sparkfun/Spectacle_Motion_Board/Firmware/Spectacle_Servo_Control_Board/Spectacle_Servo_Control_Board.cydsn/codegentemp/EZI2C_PINS.h

/***************************************************************************//**
* \file EZI2C_PINS.h
* \version 3.20
*
* \brief
*  This file provides constants and parameter values for the pin components
*  buried into SCB Component.
*
* Note:
*
********************************************************************************
* \copyright
* Copyright 2013-2016, Cypress Semiconductor Corporation.  All rights reserved.
* You may use this file only in accordance with the license, terms, conditions,
* disclaimers, and limitations in the end user license agreement accompanying
* the software package with which this file was provided.
*******************************************************************************/

#if !defined(CY_SCB_PINS_EZI2C_H)
#define CY_SCB_PINS_EZI2C_H

#include "cydevice_trm.h"
#include "cyfitter.h"
#include "cytypes.h"


/***************************************
*   Conditional Compilation Parameters
****************************************/

/* Unconfigured pins */
#define EZI2C_REMOVE_RX_WAKE_SCL_MOSI_PIN  (1u)
#define EZI2C_REMOVE_RX_SCL_MOSI_PIN      (1u)
#define EZI2C_REMOVE_TX_SDA_MISO_PIN      (1u)
#define EZI2C_REMOVE_CTS_SCLK_PIN      (1u)
#define EZI2C_REMOVE_RTS_SS0_PIN      (1u)
#define EZI2C_REMOVE_SS1_PIN                 (1u)
#define EZI2C_REMOVE_SS2_PIN                 (1u)
#define EZI2C_REMOVE_SS3_PIN                 (1u)

/* Mode defined pins */
#define EZI2C_REMOVE_I2C_PINS                (0u)
#define EZI2C_REMOVE_SPI_MASTER_PINS         (1u)
#define EZI2C_REMOVE_SPI_MASTER_SCLK_PIN     (1u)
#define EZI2C_REMOVE_SPI_MASTER_MOSI_PIN     (1u)
#define EZI2C_REMOVE_SPI_MASTER_MISO_PIN     (1u)
#define EZI2C_REMOVE_SPI_MASTER_SS0_PIN      (1u)
#define EZI2C_REMOVE_SPI_MASTER_SS1_PIN      (1u)
#define EZI2C_REMOVE_SPI_MASTER_SS2_PIN      (1u)
#define EZI2C_REMOVE_SPI_MASTER_SS3_PIN      (1u)
#define EZI2C_REMOVE_SPI_SLAVE_PINS          (1u)
#define EZI2C_REMOVE_SPI_SLAVE_MOSI_PIN      (1u)
#define EZI2C_REMOVE_SPI_SLAVE_MISO_PIN      (1u)
#define EZI2C_REMOVE_UART_TX_PIN             (1u)
#define EZI2C_REMOVE_UART_RX_TX_PIN          (1u)
#define EZI2C_REMOVE_UART_RX_PIN             (1u)
#define EZI2C_REMOVE_UART_RX_WAKE_PIN        (1u)
#define EZI2C_REMOVE_UART_RTS_PIN            (1u)
#define EZI2C_REMOVE_UART_CTS_PIN            (1u)

/* Unconfigured pins */
#define EZI2C_RX_WAKE_SCL_MOSI_PIN (0u == EZI2C_REMOVE_RX_WAKE_SCL_MOSI_PIN)
#define EZI2C_RX_SCL_MOSI_PIN     (0u == EZI2C_REMOVE_RX_SCL_MOSI_PIN)
#define EZI2C_TX_SDA_MISO_PIN     (0u == EZI2C_REMOVE_TX_SDA_MISO_PIN)
#define EZI2C_CTS_SCLK_PIN     (0u == EZI2C_REMOVE_CTS_SCLK_PIN)
#define EZI2C_RTS_SS0_PIN     (0u == EZI2C_REMOVE_RTS_SS0_PIN)
#define EZI2C_SS1_PIN                (0u == EZI2C_REMOVE_SS1_PIN)
#define EZI2C_SS2_PIN                (0u == EZI2C_REMOVE_SS2_PIN)
#define EZI2C_SS3_PIN                (0u == EZI2C_REMOVE_SS3_PIN)

/* Mode defined pins */
#define EZI2C_I2C_PINS               (0u == EZI2C_REMOVE_I2C_PINS)
#define EZI2C_SPI_MASTER_PINS        (0u == EZI2C_REMOVE_SPI_MASTER_PINS)
#define EZI2C_SPI_MASTER_SCLK_PIN    (0u == EZI2C_REMOVE_SPI_MASTER_SCLK_PIN)
#define EZI2C_SPI_MASTER_MOSI_PIN    (0u == EZI2C_REMOVE_SPI_MASTER_MOSI_PIN)
#define EZI2C_SPI_MASTER_MISO_PIN    (0u == EZI2C_REMOVE_SPI_MASTER_MISO_PIN)
#define EZI2C_SPI_MASTER_SS0_PIN     (0u == EZI2C_REMOVE_SPI_MASTER_SS0_PIN)
#define EZI2C_SPI_MASTER_SS1_PIN     (0u == EZI2C_REMOVE_SPI_MASTER_SS1_PIN)
#define EZI2C_SPI_MASTER_SS2_PIN     (0u == EZI2C_REMOVE_SPI_MASTER_SS2_PIN)
#define EZI2C_SPI_MASTER_SS3_PIN     (0u == EZI2C_REMOVE_SPI_MASTER_SS3_PIN)
#define EZI2C_SPI_SLAVE_PINS         (0u == EZI2C_REMOVE_SPI_SLAVE_PINS)
#define EZI2C_SPI_SLAVE_MOSI_PIN     (0u == EZI2C_REMOVE_SPI_SLAVE_MOSI_PIN)
#define EZI2C_SPI_SLAVE_MISO_PIN     (0u == EZI2C_REMOVE_SPI_SLAVE_MISO_PIN)
#define EZI2C_UART_TX_PIN            (0u == EZI2C_REMOVE_UART_TX_PIN)
#define EZI2C_UART_RX_TX_PIN         (0u == EZI2C_REMOVE_UART_RX_TX_PIN)
#define EZI2C_UART_RX_PIN            (0u == EZI2C_REMOVE_UART_RX_PIN)
#define EZI2C_UART_RX_WAKE_PIN       (0u == EZI2C_REMOVE_UART_RX_WAKE_PIN)
#define EZI2C_UART_RTS_PIN           (0u == EZI2C_REMOVE_UART_RTS_PIN)
#define EZI2C_UART_CTS_PIN           (0u == EZI2C_REMOVE_UART_CTS_PIN)


/***************************************
*             Includes
****************************************/

#if (EZI2C_RX_WAKE_SCL_MOSI_PIN)
    #include "EZI2C_uart_rx_wake_i2c_scl_spi_mosi.h"
#endif /* (EZI2C_RX_SCL_MOSI) */

#if (EZI2C_RX_SCL_MOSI_PIN)
    #include "EZI2C_uart_rx_i2c_scl_spi_mosi.h"
#endif /* (EZI2C_RX_SCL_MOSI) */

#if (EZI2C_TX_SDA_MISO_PIN)
    #include "EZI2C_uart_tx_i2c_sda_spi_miso.h"
#endif /* (EZI2C_TX_SDA_MISO) */

#if (EZI2C_CTS_SCLK_PIN)
    #include "EZI2C_uart_cts_spi_sclk.h"
#endif /* (EZI2C_CTS_SCLK) */

#if (EZI2C_RTS_SS0_PIN)
    #include "EZI2C_uart_rts_spi_ss0.h"
#endif /* (EZI2C_RTS_SS0_PIN) */

#if (EZI2C_SS1_PIN)
    #include "EZI2C_spi_ss1.h"
#endif /* (EZI2C_SS1_PIN) */

#if (EZI2C_SS2_PIN)
    #include "EZI2C_spi_ss2.h"
#endif /* (EZI2C_SS2_PIN) */

#if (EZI2C_SS3_PIN)
    #include "EZI2C_spi_ss3.h"
#endif /* (EZI2C_SS3_PIN) */

#if (EZI2C_I2C_PINS)
    #include "EZI2C_scl.h"
    #include "EZI2C_sda.h"
#endif /* (EZI2C_I2C_PINS) */

#if (EZI2C_SPI_MASTER_PINS)
#if (EZI2C_SPI_MASTER_SCLK_PIN)
    #include "EZI2C_sclk_m.h"
#endif /* (EZI2C_SPI_MASTER_SCLK_PIN) */

#if (EZI2C_SPI_MASTER_MOSI_PIN)
    #include "EZI2C_mosi_m.h"
#endif /* (EZI2C_SPI_MASTER_MOSI_PIN) */

#if (EZI2C_SPI_MASTER_MISO_PIN)
    #include "EZI2C_miso_m.h"
#endif /*(EZI2C_SPI_MASTER_MISO_PIN) */
#endif /* (EZI2C_SPI_MASTER_PINS) */

#if (EZI2C_SPI_SLAVE_PINS)
    #include "EZI2C_sclk_s.h"
    #include "EZI2C_ss_s.h"

#if (EZI2C_SPI_SLAVE_MOSI_PIN)
    #include "EZI2C_mosi_s.h"
#endif /* (EZI2C_SPI_SLAVE_MOSI_PIN) */

#if (EZI2C_SPI_SLAVE_MISO_PIN)
    #include "EZI2C_miso_s.h"
#endif /*(EZI2C_SPI_SLAVE_MISO_PIN) */
#endif /* (EZI2C_SPI_SLAVE_PINS) */

#if (EZI2C_SPI_MASTER_SS0_PIN)
    #include "EZI2C_ss0_m.h"
#endif /* (EZI2C_SPI_MASTER_SS0_PIN) */

#if (EZI2C_SPI_MASTER_SS1_PIN)
    #include "EZI2C_ss1_m.h"
#endif /* (EZI2C_SPI_MASTER_SS1_PIN) */

#if (EZI2C_SPI_MASTER_SS2_PIN)
    #include "EZI2C_ss2_m.h"
#endif /* (EZI2C_SPI_MASTER_SS2_PIN) */

#if (EZI2C_SPI_MASTER_SS3_PIN)
    #include "EZI2C_ss3_m.h"
#endif /* (EZI2C_SPI_MASTER_SS3_PIN) */

#if (EZI2C_UART_TX_PIN)
    #include "EZI2C_tx.h"
#endif /* (EZI2C_UART_TX_PIN) */

#if (EZI2C_UART_RX_TX_PIN)
    #include "EZI2C_rx_tx.h"
#endif /* (EZI2C_UART_RX_TX_PIN) */

#if (EZI2C_UART_RX_PIN)
    #include "EZI2C_rx.h"
#endif /* (EZI2C_UART_RX_PIN) */

#if (EZI2C_UART_RX_WAKE_PIN)
    #include "EZI2C_rx_wake.h"
#endif /* (EZI2C_UART_RX_WAKE_PIN) */

#if (EZI2C_UART_RTS_PIN)
    #include "EZI2C_rts.h"
#endif /* (EZI2C_UART_RTS_PIN) */

#if (EZI2C_UART_CTS_PIN)
    #include "EZI2C_cts.h"
#endif /* (EZI2C_UART_CTS_PIN) */


/***************************************
*              Registers
***************************************/

#if (EZI2C_RX_SCL_MOSI_PIN)
    #define EZI2C_RX_SCL_MOSI_HSIOM_REG   (*(reg32 *) EZI2C_uart_rx_i2c_scl_spi_mosi__0__HSIOM)
    #define EZI2C_RX_SCL_MOSI_HSIOM_PTR   ( (reg32 *) EZI2C_uart_rx_i2c_scl_spi_mosi__0__HSIOM)
    
    #define EZI2C_RX_SCL_MOSI_HSIOM_MASK      (EZI2C_uart_rx_i2c_scl_spi_mosi__0__HSIOM_MASK)
    #define EZI2C_RX_SCL_MOSI_HSIOM_POS       (EZI2C_uart_rx_i2c_scl_spi_mosi__0__HSIOM_SHIFT)
    #define EZI2C_RX_SCL_MOSI_HSIOM_SEL_GPIO  (EZI2C_uart_rx_i2c_scl_spi_mosi__0__HSIOM_GPIO)
    #define EZI2C_RX_SCL_MOSI_HSIOM_SEL_I2C   (EZI2C_uart_rx_i2c_scl_spi_mosi__0__HSIOM_I2C)
    #define EZI2C_RX_SCL_MOSI_HSIOM_SEL_SPI   (EZI2C_uart_rx_i2c_scl_spi_mosi__0__HSIOM_SPI)
    #define EZI2C_RX_SCL_MOSI_HSIOM_SEL_UART  (EZI2C_uart_rx_i2c_scl_spi_mosi__0__HSIOM_UART)
    
#elif (EZI2C_RX_WAKE_SCL_MOSI_PIN)
    #define EZI2C_RX_WAKE_SCL_MOSI_HSIOM_REG   (*(reg32 *) EZI2C_uart_rx_wake_i2c_scl_spi_mosi__0__HSIOM)
    #define EZI2C_RX_WAKE_SCL_MOSI_HSIOM_PTR   ( (reg32 *) EZI2C_uart_rx_wake_i2c_scl_spi_mosi__0__HSIOM)
    
    #define EZI2C_RX_WAKE_SCL_MOSI_HSIOM_MASK      (EZI2C_uart_rx_wake_i2c_scl_spi_mosi__0__HSIOM_MASK)
    #define EZI2C_RX_WAKE_SCL_MOSI_HSIOM_POS       (EZI2C_uart_rx_wake_i2c_scl_spi_mosi__0__HSIOM_SHIFT)
    #define EZI2C_RX_WAKE_SCL_MOSI_HSIOM_SEL_GPIO  (EZI2C_uart_rx_wake_i2c_scl_spi_mosi__0__HSIOM_GPIO)
    #define EZI2C_RX_WAKE_SCL_MOSI_HSIOM_SEL_I2C   (EZI2C_uart_rx_wake_i2c_scl_spi_mosi__0__HSIOM_I2C)
    #define EZI2C_RX_WAKE_SCL_MOSI_HSIOM_SEL_SPI   (EZI2C_uart_rx_wake_i2c_scl_spi_mosi__0__HSIOM_SPI)
    #define EZI2C_RX_WAKE_SCL_MOSI_HSIOM_SEL_UART  (EZI2C_uart_rx_wake_i2c_scl_spi_mosi__0__HSIOM_UART)    
   
    #define EZI2C_RX_WAKE_SCL_MOSI_INTCFG_REG (*(reg32 *) EZI2C_uart_rx_wake_i2c_scl_spi_mosi__0__INTCFG)
    #define EZI2C_RX_WAKE_SCL_MOSI_INTCFG_PTR ( (reg32 *) EZI2C_uart_rx_wake_i2c_scl_spi_mosi__0__INTCFG)
    #define EZI2C_RX_WAKE_SCL_MOSI_INTCFG_TYPE_POS  (EZI2C_uart_rx_wake_i2c_scl_spi_mosi__SHIFT)
    #define EZI2C_RX_WAKE_SCL_MOSI_INTCFG_TYPE_MASK ((uint32) EZI2C_INTCFG_TYPE_MASK << \
                                                                           EZI2C_RX_WAKE_SCL_MOSI_INTCFG_TYPE_POS)
#else
    /* None of pins EZI2C_RX_SCL_MOSI_PIN or EZI2C_RX_WAKE_SCL_MOSI_PIN present.*/
#endif /* (EZI2C_RX_SCL_MOSI_PIN) */

#if (EZI2C_TX_SDA_MISO_PIN)
    #define EZI2C_TX_SDA_MISO_HSIOM_REG   (*(reg32 *) EZI2C_uart_tx_i2c_sda_spi_miso__0__HSIOM)
    #define EZI2C_TX_SDA_MISO_HSIOM_PTR   ( (reg32 *) EZI2C_uart_tx_i2c_sda_spi_miso__0__HSIOM)
    
    #define EZI2C_TX_SDA_MISO_HSIOM_MASK      (EZI2C_uart_tx_i2c_sda_spi_miso__0__HSIOM_MASK)
    #define EZI2C_TX_SDA_MISO_HSIOM_POS       (EZI2C_uart_tx_i2c_sda_spi_miso__0__HSIOM_SHIFT)
    #define EZI2C_TX_SDA_MISO_HSIOM_SEL_GPIO  (EZI2C_uart_tx_i2c_sda_spi_miso__0__HSIOM_GPIO)
    #define EZI2C_TX_SDA_MISO_HSIOM_SEL_I2C   (EZI2C_uart_tx_i2c_sda_spi_miso__0__HSIOM_I2C)
    #define EZI2C_TX_SDA_MISO_HSIOM_SEL_SPI   (EZI2C_uart_tx_i2c_sda_spi_miso__0__HSIOM_SPI)
    #define EZI2C_TX_SDA_MISO_HSIOM_SEL_UART  (EZI2C_uart_tx_i2c_sda_spi_miso__0__HSIOM_UART)
#endif /* (EZI2C_TX_SDA_MISO_PIN) */

#if (EZI2C_CTS_SCLK_PIN)
    #define EZI2C_CTS_SCLK_HSIOM_REG   (*(reg32 *) EZI2C_uart_cts_spi_sclk__0__HSIOM)
    #define EZI2C_CTS_SCLK_HSIOM_PTR   ( (reg32 *) EZI2C_uart_cts_spi_sclk__0__HSIOM)
    
    #define EZI2C_CTS_SCLK_HSIOM_MASK      (EZI2C_uart_cts_spi_sclk__0__HSIOM_MASK)
    #define EZI2C_CTS_SCLK_HSIOM_POS       (EZI2C_uart_cts_spi_sclk__0__HSIOM_SHIFT)
    #define EZI2C_CTS_SCLK_HSIOM_SEL_GPIO  (EZI2C_uart_cts_spi_sclk__0__HSIOM_GPIO)
    #define EZI2C_CTS_SCLK_HSIOM_SEL_I2C   (EZI2C_uart_cts_spi_sclk__0__HSIOM_I2C)
    #define EZI2C_CTS_SCLK_HSIOM_SEL_SPI   (EZI2C_uart_cts_spi_sclk__0__HSIOM_SPI)
    #define EZI2C_CTS_SCLK_HSIOM_SEL_UART  (EZI2C_uart_cts_spi_sclk__0__HSIOM_UART)
#endif /* (EZI2C_CTS_SCLK_PIN) */

#if (EZI2C_RTS_SS0_PIN)
    #define EZI2C_RTS_SS0_HSIOM_REG   (*(reg32 *) EZI2C_uart_rts_spi_ss0__0__HSIOM)
    #define EZI2C_RTS_SS0_HSIOM_PTR   ( (reg32 *) EZI2C_uart_rts_spi_ss0__0__HSIOM)
    
    #define EZI2C_RTS_SS0_HSIOM_MASK      (EZI2C_uart_rts_spi_ss0__0__HSIOM_MASK)
    #define EZI2C_RTS_SS0_HSIOM_POS       (EZI2C_uart_rts_spi_ss0__0__HSIOM_SHIFT)
    #define EZI2C_RTS_SS0_HSIOM_SEL_GPIO  (EZI2C_uart_rts_spi_ss0__0__HSIOM_GPIO)
    #define EZI2C_RTS_SS0_HSIOM_SEL_I2C   (EZI2C_uart_rts_spi_ss0__0__HSIOM_I2C)
    #define EZI2C_RTS_SS0_HSIOM_SEL_SPI   (EZI2C_uart_rts_spi_ss0__0__HSIOM_SPI)
#if !(EZI2C_CY_SCBIP_V0 || EZI2C_CY_SCBIP_V1)
    #define EZI2C_RTS_SS0_HSIOM_SEL_UART  (EZI2C_uart_rts_spi_ss0__0__HSIOM_UART)
#endif /* !(EZI2C_CY_SCBIP_V0 || EZI2C_CY_SCBIP_V1) */
#endif /* (EZI2C_RTS_SS0_PIN) */

#if (EZI2C_SS1_PIN)
    #define EZI2C_SS1_HSIOM_REG  (*(reg32 *) EZI2C_spi_ss1__0__HSIOM)
    #define EZI2C_SS1_HSIOM_PTR  ( (reg32 *) EZI2C_spi_ss1__0__HSIOM)
    
    #define EZI2C_SS1_HSIOM_MASK     (EZI2C_spi_ss1__0__HSIOM_MASK)
    #define EZI2C_SS1_HSIOM_POS      (EZI2C_spi_ss1__0__HSIOM_SHIFT)
    #define EZI2C_SS1_HSIOM_SEL_GPIO (EZI2C_spi_ss1__0__HSIOM_GPIO)
    #define EZI2C_SS1_HSIOM_SEL_I2C  (EZI2C_spi_ss1__0__HSIOM_I2C)
    #define EZI2C_SS1_HSIOM_SEL_SPI  (EZI2C_spi_ss1__0__HSIOM_SPI)
#endif /* (EZI2C_SS1_PIN) */

#if (EZI2C_SS2_PIN)
    #define EZI2C_SS2_HSIOM_REG     (*(reg32 *) EZI2C_spi_ss2__0__HSIOM)
    #define EZI2C_SS2_HSIOM_PTR     ( (reg32 *) EZI2C_spi_ss2__0__HSIOM)
    
    #define EZI2C_SS2_HSIOM_MASK     (EZI2C_spi_ss2__0__HSIOM_MASK)
    #define EZI2C_SS2_HSIOM_POS      (EZI2C_spi_ss2__0__HSIOM_SHIFT)
    #define EZI2C_SS2_HSIOM_SEL_GPIO (EZI2C_spi_ss2__0__HSIOM_GPIO)
    #define EZI2C_SS2_HSIOM_SEL_I2C  (EZI2C_spi_ss2__0__HSIOM_I2C)
    #define EZI2C_SS2_HSIOM_SEL_SPI  (EZI2C_spi_ss2__0__HSIOM_SPI)
#endif /* (EZI2C_SS2_PIN) */

#if (EZI2C_SS3_PIN)
    #define EZI2C_SS3_HSIOM_REG     (*(reg32 *) EZI2C_spi_ss3__0__HSIOM)
    #define EZI2C_SS3_HSIOM_PTR     ( (reg32 *) EZI2C_spi_ss3__0__HSIOM)
    
    #define EZI2C_SS3_HSIOM_MASK     (EZI2C_spi_ss3__0__HSIOM_MASK)
    #define EZI2C_SS3_HSIOM_POS      (EZI2C_spi_ss3__0__HSIOM_SHIFT)
    #define EZI2C_SS3_HSIOM_SEL_GPIO (EZI2C_spi_ss3__0__HSIOM_GPIO)
    #define EZI2C_SS3_HSIOM_SEL_I2C  (EZI2C_spi_ss3__0__HSIOM_I2C)
    #define EZI2C_SS3_HSIOM_SEL_SPI  (EZI2C_spi_ss3__0__HSIOM_SPI)
#endif /* (EZI2C_SS3_PIN) */

#if (EZI2C_I2C_PINS)
    #define EZI2C_SCL_HSIOM_REG  (*(reg32 *) EZI2C_scl__0__HSIOM)
    #define EZI2C_SCL_HSIOM_PTR  ( (reg32 *) EZI2C_scl__0__HSIOM)
    
    #define EZI2C_SCL_HSIOM_MASK     (EZI2C_scl__0__HSIOM_MASK)
    #define EZI2C_SCL_HSIOM_POS      (EZI2C_scl__0__HSIOM_SHIFT)
    #define EZI2C_SCL_HSIOM_SEL_GPIO (EZI2C_sda__0__HSIOM_GPIO)
    #define EZI2C_SCL_HSIOM_SEL_I2C  (EZI2C_sda__0__HSIOM_I2C)
    
    #define EZI2C_SDA_HSIOM_REG  (*(reg32 *) EZI2C_sda__0__HSIOM)
    #define EZI2C_SDA_HSIOM_PTR  ( (reg32 *) EZI2C_sda__0__HSIOM)
    
    #define EZI2C_SDA_HSIOM_MASK     (EZI2C_sda__0__HSIOM_MASK)
    #define EZI2C_SDA_HSIOM_POS      (EZI2C_sda__0__HSIOM_SHIFT)
    #define EZI2C_SDA_HSIOM_SEL_GPIO (EZI2C_sda__0__HSIOM_GPIO)
    #define EZI2C_SDA_HSIOM_SEL_I2C  (EZI2C_sda__0__HSIOM_I2C)
#endif /* (EZI2C_I2C_PINS) */

#if (EZI2C_SPI_SLAVE_PINS)
    #define EZI2C_SCLK_S_HSIOM_REG   (*(reg32 *) EZI2C_sclk_s__0__HSIOM)
    #define EZI2C_SCLK_S_HSIOM_PTR   ( (reg32 *) EZI2C_sclk_s__0__HSIOM)
    
    #define EZI2C_SCLK_S_HSIOM_MASK      (EZI2C_sclk_s__0__HSIOM_MASK)
    #define EZI2C_SCLK_S_HSIOM_POS       (EZI2C_sclk_s__0__HSIOM_SHIFT)
    #define EZI2C_SCLK_S_HSIOM_SEL_GPIO  (EZI2C_sclk_s__0__HSIOM_GPIO)
    #define EZI2C_SCLK_S_HSIOM_SEL_SPI   (EZI2C_sclk_s__0__HSIOM_SPI)
    
    #define EZI2C_SS0_S_HSIOM_REG    (*(reg32 *) EZI2C_ss0_s__0__HSIOM)
    #define EZI2C_SS0_S_HSIOM_PTR    ( (reg32 *) EZI2C_ss0_s__0__HSIOM)
    
    #define EZI2C_SS0_S_HSIOM_MASK       (EZI2C_ss0_s__0__HSIOM_MASK)
    #define EZI2C_SS0_S_HSIOM_POS        (EZI2C_ss0_s__0__HSIOM_SHIFT)
    #define EZI2C_SS0_S_HSIOM_SEL_GPIO   (EZI2C_ss0_s__0__HSIOM_GPIO)  
    #define EZI2C_SS0_S_HSIOM_SEL_SPI    (EZI2C_ss0_s__0__HSIOM_SPI)
#endif /* (EZI2C_SPI_SLAVE_PINS) */

#if (EZI2C_SPI_SLAVE_MOSI_PIN)
    #define EZI2C_MOSI_S_HSIOM_REG   (*(reg32 *) EZI2C_mosi_s__0__HSIOM)
    #define EZI2C_MOSI_S_HSIOM_PTR   ( (reg32 *) EZI2C_mosi_s__0__HSIOM)
    
    #define EZI2C_MOSI_S_HSIOM_MASK      (EZI2C_mosi_s__0__HSIOM_MASK)
    #define EZI2C_MOSI_S_HSIOM_POS       (EZI2C_mosi_s__0__HSIOM_SHIFT)
    #define EZI2C_MOSI_S_HSIOM_SEL_GPIO  (EZI2C_mosi_s__0__HSIOM_GPIO)
    #define EZI2C_MOSI_S_HSIOM_SEL_SPI   (EZI2C_mosi_s__0__HSIOM_SPI)
#endif /* (EZI2C_SPI_SLAVE_MOSI_PIN) */

#if (EZI2C_SPI_SLAVE_MISO_PIN)
    #define EZI2C_MISO_S_HSIOM_REG   (*(reg32 *) EZI2C_miso_s__0__HSIOM)
    #define EZI2C_MISO_S_HSIOM_PTR   ( (reg32 *) EZI2C_miso_s__0__HSIOM)
    
    #define EZI2C_MISO_S_HSIOM_MASK      (EZI2C_miso_s__0__HSIOM_MASK)
    #define EZI2C_MISO_S_HSIOM_POS       (EZI2C_miso_s__0__HSIOM_SHIFT)
    #define EZI2C_MISO_S_HSIOM_SEL_GPIO  (EZI2C_miso_s__0__HSIOM_GPIO)
    #define EZI2C_MISO_S_HSIOM_SEL_SPI   (EZI2C_miso_s__0__HSIOM_SPI)
#endif /* (EZI2C_SPI_SLAVE_MISO_PIN) */

#if (EZI2C_SPI_MASTER_MISO_PIN)
    #define EZI2C_MISO_M_HSIOM_REG   (*(reg32 *) EZI2C_miso_m__0__HSIOM)
    #define EZI2C_MISO_M_HSIOM_PTR   ( (reg32 *) EZI2C_miso_m__0__HSIOM)
    
    #define EZI2C_MISO_M_HSIOM_MASK      (EZI2C_miso_m__0__HSIOM_MASK)
    #define EZI2C_MISO_M_HSIOM_POS       (EZI2C_miso_m__0__HSIOM_SHIFT)
    #define EZI2C_MISO_M_HSIOM_SEL_GPIO  (EZI2C_miso_m__0__HSIOM_GPIO)
    #define EZI2C_MISO_M_HSIOM_SEL_SPI   (EZI2C_miso_m__0__HSIOM_SPI)
#endif /* (EZI2C_SPI_MASTER_MISO_PIN) */

#if (EZI2C_SPI_MASTER_MOSI_PIN)
    #define EZI2C_MOSI_M_HSIOM_REG   (*(reg32 *) EZI2C_mosi_m__0__HSIOM)
    #define EZI2C_MOSI_M_HSIOM_PTR   ( (reg32 *) EZI2C_mosi_m__0__HSIOM)
    
    #define EZI2C_MOSI_M_HSIOM_MASK      (EZI2C_mosi_m__0__HSIOM_MASK)
    #define EZI2C_MOSI_M_HSIOM_POS       (EZI2C_mosi_m__0__HSIOM_SHIFT)
    #define EZI2C_MOSI_M_HSIOM_SEL_GPIO  (EZI2C_mosi_m__0__HSIOM_GPIO)
    #define EZI2C_MOSI_M_HSIOM_SEL_SPI   (EZI2C_mosi_m__0__HSIOM_SPI)
#endif /* (EZI2C_SPI_MASTER_MOSI_PIN) */

#if (EZI2C_SPI_MASTER_SCLK_PIN)
    #define EZI2C_SCLK_M_HSIOM_REG   (*(reg32 *) EZI2C_sclk_m__0__HSIOM)
    #define EZI2C_SCLK_M_HSIOM_PTR   ( (reg32 *) EZI2C_sclk_m__0__HSIOM)
    
    #define EZI2C_SCLK_M_HSIOM_MASK      (EZI2C_sclk_m__0__HSIOM_MASK)
    #define EZI2C_SCLK_M_HSIOM_POS       (EZI2C_sclk_m__0__HSIOM_SHIFT)
    #define EZI2C_SCLK_M_HSIOM_SEL_GPIO  (EZI2C_sclk_m__0__HSIOM_GPIO)
    #define EZI2C_SCLK_M_HSIOM_SEL_SPI   (EZI2C_sclk_m__0__HSIOM_SPI)
#endif /* (EZI2C_SPI_MASTER_SCLK_PIN) */

#if (EZI2C_SPI_MASTER_SS0_PIN)
    #define EZI2C_SS0_M_HSIOM_REG    (*(reg32 *) EZI2C_ss0_m__0__HSIOM)
    #define EZI2C_SS0_M_HSIOM_PTR    ( (reg32 *) EZI2C_ss0_m__0__HSIOM)
    
    #define EZI2C_SS0_M_HSIOM_MASK       (EZI2C_ss0_m__0__HSIOM_MASK)
    #define EZI2C_SS0_M_HSIOM_POS        (EZI2C_ss0_m__0__HSIOM_SHIFT)
    #define EZI2C_SS0_M_HSIOM_SEL_GPIO   (EZI2C_ss0_m__0__HSIOM_GPIO)
    #define EZI2C_SS0_M_HSIOM_SEL_SPI    (EZI2C_ss0_m__0__HSIOM_SPI)
#endif /* (EZI2C_SPI_MASTER_SS0_PIN) */

#if (EZI2C_SPI_MASTER_SS1_PIN)
    #define EZI2C_SS1_M_HSIOM_REG    (*(reg32 *) EZI2C_ss1_m__0__HSIOM)
    #define EZI2C_SS1_M_HSIOM_PTR    ( (reg32 *) EZI2C_ss1_m__0__HSIOM)
    
    #define EZI2C_SS1_M_HSIOM_MASK       (EZI2C_ss1_m__0__HSIOM_MASK)
    #define EZI2C_SS1_M_HSIOM_POS        (EZI2C_ss1_m__0__HSIOM_SHIFT)
    #define EZI2C_SS1_M_HSIOM_SEL_GPIO   (EZI2C_ss1_m__0__HSIOM_GPIO)
    #define EZI2C_SS1_M_HSIOM_SEL_SPI    (EZI2C_ss1_m__0__HSIOM_SPI)
#endif /* (EZI2C_SPI_MASTER_SS1_PIN) */

#if (EZI2C_SPI_MASTER_SS2_PIN)
    #define EZI2C_SS2_M_HSIOM_REG    (*(reg32 *) EZI2C_ss2_m__0__HSIOM)
    #define EZI2C_SS2_M_HSIOM_PTR    ( (reg32 *) EZI2C_ss2_m__0__HSIOM)
    
    #define EZI2C_SS2_M_HSIOM_MASK       (EZI2C_ss2_m__0__HSIOM_MASK)
    #define EZI2C_SS2_M_HSIOM_POS        (EZI2C_ss2_m__0__HSIOM_SHIFT)
    #define EZI2C_SS2_M_HSIOM_SEL_GPIO   (EZI2C_ss2_m__0__HSIOM_GPIO)
    #define EZI2C_SS2_M_HSIOM_SEL_SPI    (EZI2C_ss2_m__0__HSIOM_SPI)
#endif /* (EZI2C_SPI_MASTER_SS2_PIN) */

#if (EZI2C_SPI_MASTER_SS3_PIN)
    #define EZI2C_SS3_M_HSIOM_REG    (*(reg32 *) EZI2C_ss3_m__0__HSIOM)
    #define EZI2C_SS3_M_HSIOM_PTR    ( (reg32 *) EZI2C_ss3_m__0__HSIOM)
    
    #define EZI2C_SS3_M_HSIOM_MASK      (EZI2C_ss3_m__0__HSIOM_MASK)
    #define EZI2C_SS3_M_HSIOM_POS       (EZI2C_ss3_m__0__HSIOM_SHIFT)
    #define EZI2C_SS3_M_HSIOM_SEL_GPIO  (EZI2C_ss3_m__0__HSIOM_GPIO)
    #define EZI2C_SS3_M_HSIOM_SEL_SPI   (EZI2C_ss3_m__0__HSIOM_SPI)
#endif /* (EZI2C_SPI_MASTER_SS3_PIN) */

#if (EZI2C_UART_RX_PIN)
    #define EZI2C_RX_HSIOM_REG   (*(reg32 *) EZI2C_rx__0__HSIOM)
    #define EZI2C_RX_HSIOM_PTR   ( (reg32 *) EZI2C_rx__0__HSIOM)
    
    #define EZI2C_RX_HSIOM_MASK      (EZI2C_rx__0__HSIOM_MASK)
    #define EZI2C_RX_HSIOM_POS       (EZI2C_rx__0__HSIOM_SHIFT)
    #define EZI2C_RX_HSIOM_SEL_GPIO  (EZI2C_rx__0__HSIOM_GPIO)
    #define EZI2C_RX_HSIOM_SEL_UART  (EZI2C_rx__0__HSIOM_UART)
#endif /* (EZI2C_UART_RX_PIN) */

#if (EZI2C_UART_RX_WAKE_PIN)
    #define EZI2C_RX_WAKE_HSIOM_REG   (*(reg32 *) EZI2C_rx_wake__0__HSIOM)
    #define EZI2C_RX_WAKE_HSIOM_PTR   ( (reg32 *) EZI2C_rx_wake__0__HSIOM)
    
    #define EZI2C_RX_WAKE_HSIOM_MASK      (EZI2C_rx_wake__0__HSIOM_MASK)
    #define EZI2C_RX_WAKE_HSIOM_POS       (EZI2C_rx_wake__0__HSIOM_SHIFT)
    #define EZI2C_RX_WAKE_HSIOM_SEL_GPIO  (EZI2C_rx_wake__0__HSIOM_GPIO)
    #define EZI2C_RX_WAKE_HSIOM_SEL_UART  (EZI2C_rx_wake__0__HSIOM_UART)
#endif /* (EZI2C_UART_WAKE_RX_PIN) */

#if (EZI2C_UART_CTS_PIN)
    #define EZI2C_CTS_HSIOM_REG   (*(reg32 *) EZI2C_cts__0__HSIOM)
    #define EZI2C_CTS_HSIOM_PTR   ( (reg32 *) EZI2C_cts__0__HSIOM)
    
    #define EZI2C_CTS_HSIOM_MASK      (EZI2C_cts__0__HSIOM_MASK)
    #define EZI2C_CTS_HSIOM_POS       (EZI2C_cts__0__HSIOM_SHIFT)
    #define EZI2C_CTS_HSIOM_SEL_GPIO  (EZI2C_cts__0__HSIOM_GPIO)
    #define EZI2C_CTS_HSIOM_SEL_UART  (EZI2C_cts__0__HSIOM_UART)
#endif /* (EZI2C_UART_CTS_PIN) */

#if (EZI2C_UART_TX_PIN)
    #define EZI2C_TX_HSIOM_REG   (*(reg32 *) EZI2C_tx__0__HSIOM)
    #define EZI2C_TX_HSIOM_PTR   ( (reg32 *) EZI2C_tx__0__HSIOM)
    
    #define EZI2C_TX_HSIOM_MASK      (EZI2C_tx__0__HSIOM_MASK)
    #define EZI2C_TX_HSIOM_POS       (EZI2C_tx__0__HSIOM_SHIFT)
    #define EZI2C_TX_HSIOM_SEL_GPIO  (EZI2C_tx__0__HSIOM_GPIO)
    #define EZI2C_TX_HSIOM_SEL_UART  (EZI2C_tx__0__HSIOM_UART)
#endif /* (EZI2C_UART_TX_PIN) */

#if (EZI2C_UART_RX_TX_PIN)
    #define EZI2C_RX_TX_HSIOM_REG   (*(reg32 *) EZI2C_rx_tx__0__HSIOM)
    #define EZI2C_RX_TX_HSIOM_PTR   ( (reg32 *) EZI2C_rx_tx__0__HSIOM)
    
    #define EZI2C_RX_TX_HSIOM_MASK      (EZI2C_rx_tx__0__HSIOM_MASK)
    #define EZI2C_RX_TX_HSIOM_POS       (EZI2C_rx_tx__0__HSIOM_SHIFT)
    #define EZI2C_RX_TX_HSIOM_SEL_GPIO  (EZI2C_rx_tx__0__HSIOM_GPIO)
    #define EZI2C_RX_TX_HSIOM_SEL_UART  (EZI2C_rx_tx__0__HSIOM_UART)
#endif /* (EZI2C_UART_RX_TX_PIN) */

#if (EZI2C_UART_RTS_PIN)
    #define EZI2C_RTS_HSIOM_REG      (*(reg32 *) EZI2C_rts__0__HSIOM)
    #define EZI2C_RTS_HSIOM_PTR      ( (reg32 *) EZI2C_rts__0__HSIOM)
    
    #define EZI2C_RTS_HSIOM_MASK     (EZI2C_rts__0__HSIOM_MASK)
    #define EZI2C_RTS_HSIOM_POS      (EZI2C_rts__0__HSIOM_SHIFT)    
    #define EZI2C_RTS_HSIOM_SEL_GPIO (EZI2C_rts__0__HSIOM_GPIO)
    #define EZI2C_RTS_HSIOM_SEL_UART (EZI2C_rts__0__HSIOM_UART)    
#endif /* (EZI2C_UART_RTS_PIN) */


/***************************************
*        Registers Constants
***************************************/

/* HSIOM switch values. */ 
#define EZI2C_HSIOM_DEF_SEL      (0x00u)
#define EZI2C_HSIOM_GPIO_SEL     (0x00u)
/* The HSIOM values provided below are valid only for EZI2C_CY_SCBIP_V0 
* and EZI2C_CY_SCBIP_V1. It is not recommended to use them for 
* EZI2C_CY_SCBIP_V2. Use pin name specific HSIOM constants provided 
* above instead for any SCB IP block version.
*/
#define EZI2C_HSIOM_UART_SEL     (0x09u)
#define EZI2C_HSIOM_I2C_SEL      (0x0Eu)
#define EZI2C_HSIOM_SPI_SEL      (0x0Fu)

/* Pins settings index. */
#define EZI2C_RX_WAKE_SCL_MOSI_PIN_INDEX   (0u)
#define EZI2C_RX_SCL_MOSI_PIN_INDEX       (0u)
#define EZI2C_TX_SDA_MISO_PIN_INDEX       (1u)
#define EZI2C_CTS_SCLK_PIN_INDEX       (2u)
#define EZI2C_RTS_SS0_PIN_INDEX       (3u)
#define EZI2C_SS1_PIN_INDEX                  (4u)
#define EZI2C_SS2_PIN_INDEX                  (5u)
#define EZI2C_SS3_PIN_INDEX                  (6u)

/* Pins settings mask. */
#define EZI2C_RX_WAKE_SCL_MOSI_PIN_MASK ((uint32) 0x01u << EZI2C_RX_WAKE_SCL_MOSI_PIN_INDEX)
#define EZI2C_RX_SCL_MOSI_PIN_MASK     ((uint32) 0x01u << EZI2C_RX_SCL_MOSI_PIN_INDEX)
#define EZI2C_TX_SDA_MISO_PIN_MASK     ((uint32) 0x01u << EZI2C_TX_SDA_MISO_PIN_INDEX)
#define EZI2C_CTS_SCLK_PIN_MASK     ((uint32) 0x01u << EZI2C_CTS_SCLK_PIN_INDEX)
#define EZI2C_RTS_SS0_PIN_MASK     ((uint32) 0x01u << EZI2C_RTS_SS0_PIN_INDEX)
#define EZI2C_SS1_PIN_MASK                ((uint32) 0x01u << EZI2C_SS1_PIN_INDEX)
#define EZI2C_SS2_PIN_MASK                ((uint32) 0x01u << EZI2C_SS2_PIN_INDEX)
#define EZI2C_SS3_PIN_MASK                ((uint32) 0x01u << EZI2C_SS3_PIN_INDEX)

/* Pin interrupt constants. */
#define EZI2C_INTCFG_TYPE_MASK           (0x03u)
#define EZI2C_INTCFG_TYPE_FALLING_EDGE   (0x02u)

/* Pin Drive Mode constants. */
#define EZI2C_PIN_DM_ALG_HIZ  (0u)
#define EZI2C_PIN_DM_DIG_HIZ  (1u)
#define EZI2C_PIN_DM_OD_LO    (4u)
#define EZI2C_PIN_DM_STRONG   (6u)


/***************************************
*          Macro Definitions
***************************************/

/* Return drive mode of the pin */
#define EZI2C_DM_MASK    (0x7u)
#define EZI2C_DM_SIZE    (3u)
#define EZI2C_GET_P4_PIN_DM(reg, pos) \
    ( ((reg) & (uint32) ((uint32) EZI2C_DM_MASK << (EZI2C_DM_SIZE * (pos)))) >> \
                                                              (EZI2C_DM_SIZE * (pos)) )

#if (EZI2C_TX_SDA_MISO_PIN)
    #define EZI2C_CHECK_TX_SDA_MISO_PIN_USED \
                (EZI2C_PIN_DM_ALG_HIZ != \
                    EZI2C_GET_P4_PIN_DM(EZI2C_uart_tx_i2c_sda_spi_miso_PC, \
                                                   EZI2C_uart_tx_i2c_sda_spi_miso_SHIFT))
#endif /* (EZI2C_TX_SDA_MISO_PIN) */

#if (EZI2C_RTS_SS0_PIN)
    #define EZI2C_CHECK_RTS_SS0_PIN_USED \
                (EZI2C_PIN_DM_ALG_HIZ != \
                    EZI2C_GET_P4_PIN_DM(EZI2C_uart_rts_spi_ss0_PC, \
                                                   EZI2C_uart_rts_spi_ss0_SHIFT))
#endif /* (EZI2C_RTS_SS0_PIN) */

/* Set bits-mask in register */
#define EZI2C_SET_REGISTER_BITS(reg, mask, pos, mode) \
                    do                                           \
                    {                                            \
                        (reg) = (((reg) & ((uint32) ~(uint32) (mask))) | ((uint32) ((uint32) (mode) << (pos)))); \
                    }while(0)

/* Set bit in the register */
#define EZI2C_SET_REGISTER_BIT(reg, mask, val) \
                    ((val) ? ((reg) |= (mask)) : ((reg) &= ((uint32) ~((uint32) (mask)))))

#define EZI2C_SET_HSIOM_SEL(reg, mask, pos, sel) EZI2C_SET_REGISTER_BITS(reg, mask, pos, sel)
#define EZI2C_SET_INCFG_TYPE(reg, mask, pos, intType) \
                                                        EZI2C_SET_REGISTER_BITS(reg, mask, pos, intType)
#define EZI2C_SET_INP_DIS(reg, mask, val) EZI2C_SET_REGISTER_BIT(reg, mask, val)

/* EZI2C_SET_I2C_SCL_DR(val) - Sets I2C SCL DR register.
*  EZI2C_SET_I2C_SCL_HSIOM_SEL(sel) - Sets I2C SCL HSIOM settings.
*/
/* SCB I2C: scl signal */
#if (EZI2C_CY_SCBIP_V0)
#if (EZI2C_I2C_PINS)
    #define EZI2C_SET_I2C_SCL_DR(val) EZI2C_scl_Write(val)

    #define EZI2C_SET_I2C_SCL_HSIOM_SEL(sel) \
                          EZI2C_SET_HSIOM_SEL(EZI2C_SCL_HSIOM_REG,  \
                                                         EZI2C_SCL_HSIOM_MASK, \
                                                         EZI2C_SCL_HSIOM_POS,  \
                                                         (sel))
    #define EZI2C_WAIT_SCL_SET_HIGH  (0u == EZI2C_scl_Read())

/* Unconfigured SCB: scl signal */
#elif (EZI2C_RX_WAKE_SCL_MOSI_PIN)
    #define EZI2C_SET_I2C_SCL_DR(val) \
                            EZI2C_uart_rx_wake_i2c_scl_spi_mosi_Write(val)

    #define EZI2C_SET_I2C_SCL_HSIOM_SEL(sel) \
                    EZI2C_SET_HSIOM_SEL(EZI2C_RX_WAKE_SCL_MOSI_HSIOM_REG,  \
                                                   EZI2C_RX_WAKE_SCL_MOSI_HSIOM_MASK, \
                                                   EZI2C_RX_WAKE_SCL_MOSI_HSIOM_POS,  \
                                                   (sel))

    #define EZI2C_WAIT_SCL_SET_HIGH  (0u == EZI2C_uart_rx_wake_i2c_scl_spi_mosi_Read())

#elif (EZI2C_RX_SCL_MOSI_PIN)
    #define EZI2C_SET_I2C_SCL_DR(val) \
                            EZI2C_uart_rx_i2c_scl_spi_mosi_Write(val)


    #define EZI2C_SET_I2C_SCL_HSIOM_SEL(sel) \
                            EZI2C_SET_HSIOM_SEL(EZI2C_RX_SCL_MOSI_HSIOM_REG,  \
                                                           EZI2C_RX_SCL_MOSI_HSIOM_MASK, \
                                                           EZI2C_RX_SCL_MOSI_HSIOM_POS,  \
                                                           (sel))

    #define EZI2C_WAIT_SCL_SET_HIGH  (0u == EZI2C_uart_rx_i2c_scl_spi_mosi_Read())

#else
    #define EZI2C_SET_I2C_SCL_DR(val)        do{ /* Does nothing */ }while(0)
    #define EZI2C_SET_I2C_SCL_HSIOM_SEL(sel) do{ /* Does nothing */ }while(0)

    #define EZI2C_WAIT_SCL_SET_HIGH  (0u)
#endif /* (EZI2C_I2C_PINS) */

/* SCB I2C: sda signal */
#if (EZI2C_I2C_PINS)
    #define EZI2C_WAIT_SDA_SET_HIGH  (0u == EZI2C_sda_Read())
/* Unconfigured SCB: sda signal */
#elif (EZI2C_TX_SDA_MISO_PIN)
    #define EZI2C_WAIT_SDA_SET_HIGH  (0u == EZI2C_uart_tx_i2c_sda_spi_miso_Read())
#else
    #define EZI2C_WAIT_SDA_SET_HIGH  (0u)
#endif /* (EZI2C_MOSI_SCL_RX_PIN) */
#endif /* (EZI2C_CY_SCBIP_V0) */

/* Clear UART wakeup source */
#if (EZI2C_RX_SCL_MOSI_PIN)
    #define EZI2C_CLEAR_UART_RX_WAKE_INTR        do{ /* Does nothing */ }while(0)
    
#elif (EZI2C_RX_WAKE_SCL_MOSI_PIN)
    #define EZI2C_CLEAR_UART_RX_WAKE_INTR \
            do{                                      \
                (void) EZI2C_uart_rx_wake_i2c_scl_spi_mosi_ClearInterrupt(); \
            }while(0)

#elif(EZI2C_UART_RX_WAKE_PIN)
    #define EZI2C_CLEAR_UART_RX_WAKE_INTR \
            do{                                      \
                (void) EZI2C_rx_wake_ClearInterrupt(); \
            }while(0)
#else
#endif /* (EZI2C_RX_SCL_MOSI_PIN) */


/***************************************
* The following code is DEPRECATED and
* must not be used.
***************************************/

/* Unconfigured pins */
#define EZI2C_REMOVE_MOSI_SCL_RX_WAKE_PIN    EZI2C_REMOVE_RX_WAKE_SCL_MOSI_PIN
#define EZI2C_REMOVE_MOSI_SCL_RX_PIN         EZI2C_REMOVE_RX_SCL_MOSI_PIN
#define EZI2C_REMOVE_MISO_SDA_TX_PIN         EZI2C_REMOVE_TX_SDA_MISO_PIN
#ifndef EZI2C_REMOVE_SCLK_PIN
#define EZI2C_REMOVE_SCLK_PIN                EZI2C_REMOVE_CTS_SCLK_PIN
#endif /* EZI2C_REMOVE_SCLK_PIN */
#ifndef EZI2C_REMOVE_SS0_PIN
#define EZI2C_REMOVE_SS0_PIN                 EZI2C_REMOVE_RTS_SS0_PIN
#endif /* EZI2C_REMOVE_SS0_PIN */

/* Unconfigured pins */
#define EZI2C_MOSI_SCL_RX_WAKE_PIN   EZI2C_RX_WAKE_SCL_MOSI_PIN
#define EZI2C_MOSI_SCL_RX_PIN        EZI2C_RX_SCL_MOSI_PIN
#define EZI2C_MISO_SDA_TX_PIN        EZI2C_TX_SDA_MISO_PIN
#ifndef EZI2C_SCLK_PIN
#define EZI2C_SCLK_PIN               EZI2C_CTS_SCLK_PIN
#endif /* EZI2C_SCLK_PIN */
#ifndef EZI2C_SS0_PIN
#define EZI2C_SS0_PIN                EZI2C_RTS_SS0_PIN
#endif /* EZI2C_SS0_PIN */

#if (EZI2C_MOSI_SCL_RX_WAKE_PIN)
    #define EZI2C_MOSI_SCL_RX_WAKE_HSIOM_REG     EZI2C_RX_WAKE_SCL_MOSI_HSIOM_REG
    #define EZI2C_MOSI_SCL_RX_WAKE_HSIOM_PTR     EZI2C_RX_WAKE_SCL_MOSI_HSIOM_REG
    #define EZI2C_MOSI_SCL_RX_WAKE_HSIOM_MASK    EZI2C_RX_WAKE_SCL_MOSI_HSIOM_REG
    #define EZI2C_MOSI_SCL_RX_WAKE_HSIOM_POS     EZI2C_RX_WAKE_SCL_MOSI_HSIOM_REG

    #define EZI2C_MOSI_SCL_RX_WAKE_INTCFG_REG    EZI2C_RX_WAKE_SCL_MOSI_HSIOM_REG
    #define EZI2C_MOSI_SCL_RX_WAKE_INTCFG_PTR    EZI2C_RX_WAKE_SCL_MOSI_HSIOM_REG

    #define EZI2C_MOSI_SCL_RX_WAKE_INTCFG_TYPE_POS   EZI2C_RX_WAKE_SCL_MOSI_HSIOM_REG
    #define EZI2C_MOSI_SCL_RX_WAKE_INTCFG_TYPE_MASK  EZI2C_RX_WAKE_SCL_MOSI_HSIOM_REG
#endif /* (EZI2C_RX_WAKE_SCL_MOSI_PIN) */

#if (EZI2C_MOSI_SCL_RX_PIN)
    #define EZI2C_MOSI_SCL_RX_HSIOM_REG      EZI2C_RX_SCL_MOSI_HSIOM_REG
    #define EZI2C_MOSI_SCL_RX_HSIOM_PTR      EZI2C_RX_SCL_MOSI_HSIOM_PTR
    #define EZI2C_MOSI_SCL_RX_HSIOM_MASK     EZI2C_RX_SCL_MOSI_HSIOM_MASK
    #define EZI2C_MOSI_SCL_RX_HSIOM_POS      EZI2C_RX_SCL_MOSI_HSIOM_POS
#endif /* (EZI2C_MOSI_SCL_RX_PIN) */

#if (EZI2C_MISO_SDA_TX_PIN)
    #define EZI2C_MISO_SDA_TX_HSIOM_REG      EZI2C_TX_SDA_MISO_HSIOM_REG
    #define EZI2C_MISO_SDA_TX_HSIOM_PTR      EZI2C_TX_SDA_MISO_HSIOM_REG
    #define EZI2C_MISO_SDA_TX_HSIOM_MASK     EZI2C_TX_SDA_MISO_HSIOM_REG
    #define EZI2C_MISO_SDA_TX_HSIOM_POS      EZI2C_TX_SDA_MISO_HSIOM_REG
#endif /* (EZI2C_MISO_SDA_TX_PIN_PIN) */

#if (EZI2C_SCLK_PIN)
    #ifndef EZI2C_SCLK_HSIOM_REG
    #define EZI2C_SCLK_HSIOM_REG     EZI2C_CTS_SCLK_HSIOM_REG
    #define EZI2C_SCLK_HSIOM_PTR     EZI2C_CTS_SCLK_HSIOM_PTR
    #define EZI2C_SCLK_HSIOM_MASK    EZI2C_CTS_SCLK_HSIOM_MASK
    #define EZI2C_SCLK_HSIOM_POS     EZI2C_CTS_SCLK_HSIOM_POS
    #endif /* EZI2C_SCLK_HSIOM_REG */
#endif /* (EZI2C_SCLK_PIN) */

#if (EZI2C_SS0_PIN)
    #ifndef EZI2C_SS0_HSIOM_REG
    #define EZI2C_SS0_HSIOM_REG      EZI2C_RTS_SS0_HSIOM_REG
    #define EZI2C_SS0_HSIOM_PTR      EZI2C_RTS_SS0_HSIOM_PTR
    #define EZI2C_SS0_HSIOM_MASK     EZI2C_RTS_SS0_HSIOM_MASK
    #define EZI2C_SS0_HSIOM_POS      EZI2C_RTS_SS0_HSIOM_POS
    #endif /* EZI2C_SS0_HSIOM_REG */
#endif /* (EZI2C_SS0_PIN) */

#define EZI2C_MOSI_SCL_RX_WAKE_PIN_INDEX EZI2C_RX_WAKE_SCL_MOSI_PIN_INDEX
#define EZI2C_MOSI_SCL_RX_PIN_INDEX      EZI2C_RX_SCL_MOSI_PIN_INDEX
#define EZI2C_MISO_SDA_TX_PIN_INDEX      EZI2C_TX_SDA_MISO_PIN_INDEX
#ifndef EZI2C_SCLK_PIN_INDEX
#define EZI2C_SCLK_PIN_INDEX             EZI2C_CTS_SCLK_PIN_INDEX
#endif /* EZI2C_SCLK_PIN_INDEX */
#ifndef EZI2C_SS0_PIN_INDEX
#define EZI2C_SS0_PIN_INDEX              EZI2C_RTS_SS0_PIN_INDEX
#endif /* EZI2C_SS0_PIN_INDEX */

#define EZI2C_MOSI_SCL_RX_WAKE_PIN_MASK EZI2C_RX_WAKE_SCL_MOSI_PIN_MASK
#define EZI2C_MOSI_SCL_RX_PIN_MASK      EZI2C_RX_SCL_MOSI_PIN_MASK
#define EZI2C_MISO_SDA_TX_PIN_MASK      EZI2C_TX_SDA_MISO_PIN_MASK
#ifndef EZI2C_SCLK_PIN_MASK
#define EZI2C_SCLK_PIN_MASK             EZI2C_CTS_SCLK_PIN_MASK
#endif /* EZI2C_SCLK_PIN_MASK */
#ifndef EZI2C_SS0_PIN_MASK
#define EZI2C_SS0_PIN_MASK              EZI2C_RTS_SS0_PIN_MASK
#endif /* EZI2C_SS0_PIN_MASK */

#endif /* (CY_SCB_PINS_EZI2C_H) */


/* [] END OF FILE */
