sparkfun/Spectacle_Motion_Board/Firmware/Spectacle_Servo_Control_Board/Spectacle_Servo_Control_Board.cydsn/codegentemp/cyfitter.h

#ifndef INCLUDED_CYFITTER_H
#define INCLUDED_CYFITTER_H
#include "cydevice_trm.h"

/* LED */
#define LED__0__DR CYREG_GPIO_PRT2_DR
#define LED__0__DR_CLR CYREG_GPIO_PRT2_DR_CLR
#define LED__0__DR_INV CYREG_GPIO_PRT2_DR_INV
#define LED__0__DR_SET CYREG_GPIO_PRT2_DR_SET
#define LED__0__HSIOM CYREG_HSIOM_PORT_SEL2
#define LED__0__HSIOM_MASK 0xF0000000u
#define LED__0__HSIOM_SHIFT 28u
#define LED__0__INTCFG CYREG_GPIO_PRT2_INTR_CFG
#define LED__0__INTR CYREG_GPIO_PRT2_INTR
#define LED__0__INTR_CFG CYREG_GPIO_PRT2_INTR_CFG
#define LED__0__INTSTAT CYREG_GPIO_PRT2_INTR
#define LED__0__MASK 0x80u
#define LED__0__PC CYREG_GPIO_PRT2_PC
#define LED__0__PC2 CYREG_GPIO_PRT2_PC2
#define LED__0__PORT 2u
#define LED__0__PS CYREG_GPIO_PRT2_PS
#define LED__0__SHIFT 7u
#define LED__DR CYREG_GPIO_PRT2_DR
#define LED__DR_CLR CYREG_GPIO_PRT2_DR_CLR
#define LED__DR_INV CYREG_GPIO_PRT2_DR_INV
#define LED__DR_SET CYREG_GPIO_PRT2_DR_SET
#define LED__INTCFG CYREG_GPIO_PRT2_INTR_CFG
#define LED__INTR CYREG_GPIO_PRT2_INTR
#define LED__INTR_CFG CYREG_GPIO_PRT2_INTR_CFG
#define LED__INTSTAT CYREG_GPIO_PRT2_INTR
#define LED__MASK 0x80u
#define LED__PC CYREG_GPIO_PRT2_PC
#define LED__PC2 CYREG_GPIO_PRT2_PC2
#define LED__PORT 2u
#define LED__PS CYREG_GPIO_PRT2_PS
#define LED__SHIFT 7u

/* UART_rx */
#define UART_rx__0__DR CYREG_GPIO_PRT0_DR
#define UART_rx__0__DR_CLR CYREG_GPIO_PRT0_DR_CLR
#define UART_rx__0__DR_INV CYREG_GPIO_PRT0_DR_INV
#define UART_rx__0__DR_SET CYREG_GPIO_PRT0_DR_SET
#define UART_rx__0__HSIOM CYREG_HSIOM_PORT_SEL0
#define UART_rx__0__HSIOM_GPIO 0u
#define UART_rx__0__HSIOM_I2C 14u
#define UART_rx__0__HSIOM_I2C_SCL 14u
#define UART_rx__0__HSIOM_MASK 0x000F0000u
#define UART_rx__0__HSIOM_SHIFT 16u
#define UART_rx__0__HSIOM_SPI 15u
#define UART_rx__0__HSIOM_SPI_MOSI 15u
#define UART_rx__0__HSIOM_UART 9u
#define UART_rx__0__HSIOM_UART_RX 9u
#define UART_rx__0__INTCFG CYREG_GPIO_PRT0_INTR_CFG
#define UART_rx__0__INTR CYREG_GPIO_PRT0_INTR
#define UART_rx__0__INTR_CFG CYREG_GPIO_PRT0_INTR_CFG
#define UART_rx__0__INTSTAT CYREG_GPIO_PRT0_INTR
#define UART_rx__0__MASK 0x10u
#define UART_rx__0__PC CYREG_GPIO_PRT0_PC
#define UART_rx__0__PC2 CYREG_GPIO_PRT0_PC2
#define UART_rx__0__PORT 0u
#define UART_rx__0__PS CYREG_GPIO_PRT0_PS
#define UART_rx__0__SHIFT 4u
#define UART_rx__DR CYREG_GPIO_PRT0_DR
#define UART_rx__DR_CLR CYREG_GPIO_PRT0_DR_CLR
#define UART_rx__DR_INV CYREG_GPIO_PRT0_DR_INV
#define UART_rx__DR_SET CYREG_GPIO_PRT0_DR_SET
#define UART_rx__INTCFG CYREG_GPIO_PRT0_INTR_CFG
#define UART_rx__INTR CYREG_GPIO_PRT0_INTR
#define UART_rx__INTR_CFG CYREG_GPIO_PRT0_INTR_CFG
#define UART_rx__INTSTAT CYREG_GPIO_PRT0_INTR
#define UART_rx__MASK 0x10u
#define UART_rx__PC CYREG_GPIO_PRT0_PC
#define UART_rx__PC2 CYREG_GPIO_PRT0_PC2
#define UART_rx__PORT 0u
#define UART_rx__PS CYREG_GPIO_PRT0_PS
#define UART_rx__SHIFT 4u

/* UART_SCB */
#define UART_SCB__CTRL CYREG_SCB1_CTRL
#define UART_SCB__EZ_DATA0 CYREG_SCB1_EZ_DATA0
#define UART_SCB__EZ_DATA1 CYREG_SCB1_EZ_DATA1
#define UART_SCB__EZ_DATA10 CYREG_SCB1_EZ_DATA10
#define UART_SCB__EZ_DATA11 CYREG_SCB1_EZ_DATA11
#define UART_SCB__EZ_DATA12 CYREG_SCB1_EZ_DATA12
#define UART_SCB__EZ_DATA13 CYREG_SCB1_EZ_DATA13
#define UART_SCB__EZ_DATA14 CYREG_SCB1_EZ_DATA14
#define UART_SCB__EZ_DATA15 CYREG_SCB1_EZ_DATA15
#define UART_SCB__EZ_DATA16 CYREG_SCB1_EZ_DATA16
#define UART_SCB__EZ_DATA17 CYREG_SCB1_EZ_DATA17
#define UART_SCB__EZ_DATA18 CYREG_SCB1_EZ_DATA18
#define UART_SCB__EZ_DATA19 CYREG_SCB1_EZ_DATA19
#define UART_SCB__EZ_DATA2 CYREG_SCB1_EZ_DATA2
#define UART_SCB__EZ_DATA20 CYREG_SCB1_EZ_DATA20
#define UART_SCB__EZ_DATA21 CYREG_SCB1_EZ_DATA21
#define UART_SCB__EZ_DATA22 CYREG_SCB1_EZ_DATA22
#define UART_SCB__EZ_DATA23 CYREG_SCB1_EZ_DATA23
#define UART_SCB__EZ_DATA24 CYREG_SCB1_EZ_DATA24
#define UART_SCB__EZ_DATA25 CYREG_SCB1_EZ_DATA25
#define UART_SCB__EZ_DATA26 CYREG_SCB1_EZ_DATA26
#define UART_SCB__EZ_DATA27 CYREG_SCB1_EZ_DATA27
#define UART_SCB__EZ_DATA28 CYREG_SCB1_EZ_DATA28
#define UART_SCB__EZ_DATA29 CYREG_SCB1_EZ_DATA29
#define UART_SCB__EZ_DATA3 CYREG_SCB1_EZ_DATA3
#define UART_SCB__EZ_DATA30 CYREG_SCB1_EZ_DATA30
#define UART_SCB__EZ_DATA31 CYREG_SCB1_EZ_DATA31
#define UART_SCB__EZ_DATA4 CYREG_SCB1_EZ_DATA4
#define UART_SCB__EZ_DATA5 CYREG_SCB1_EZ_DATA5
#define UART_SCB__EZ_DATA6 CYREG_SCB1_EZ_DATA6
#define UART_SCB__EZ_DATA7 CYREG_SCB1_EZ_DATA7
#define UART_SCB__EZ_DATA8 CYREG_SCB1_EZ_DATA8
#define UART_SCB__EZ_DATA9 CYREG_SCB1_EZ_DATA9
#define UART_SCB__I2C_CFG CYREG_SCB1_I2C_CFG
#define UART_SCB__I2C_CTRL CYREG_SCB1_I2C_CTRL
#define UART_SCB__I2C_M_CMD CYREG_SCB1_I2C_M_CMD
#define UART_SCB__I2C_S_CMD CYREG_SCB1_I2C_S_CMD
#define UART_SCB__I2C_STATUS CYREG_SCB1_I2C_STATUS
#define UART_SCB__INTR_CAUSE CYREG_SCB1_INTR_CAUSE
#define UART_SCB__INTR_I2C_EC CYREG_SCB1_INTR_I2C_EC
#define UART_SCB__INTR_I2C_EC_MASK CYREG_SCB1_INTR_I2C_EC_MASK
#define UART_SCB__INTR_I2C_EC_MASKED CYREG_SCB1_INTR_I2C_EC_MASKED
#define UART_SCB__INTR_M CYREG_SCB1_INTR_M
#define UART_SCB__INTR_M_MASK CYREG_SCB1_INTR_M_MASK
#define UART_SCB__INTR_M_MASKED CYREG_SCB1_INTR_M_MASKED
#define UART_SCB__INTR_M_SET CYREG_SCB1_INTR_M_SET
#define UART_SCB__INTR_RX CYREG_SCB1_INTR_RX
#define UART_SCB__INTR_RX_MASK CYREG_SCB1_INTR_RX_MASK
#define UART_SCB__INTR_RX_MASKED CYREG_SCB1_INTR_RX_MASKED
#define UART_SCB__INTR_RX_SET CYREG_SCB1_INTR_RX_SET
#define UART_SCB__INTR_S CYREG_SCB1_INTR_S
#define UART_SCB__INTR_S_MASK CYREG_SCB1_INTR_S_MASK
#define UART_SCB__INTR_S_MASKED CYREG_SCB1_INTR_S_MASKED
#define UART_SCB__INTR_S_SET CYREG_SCB1_INTR_S_SET
#define UART_SCB__INTR_SPI_EC CYREG_SCB1_INTR_SPI_EC
#define UART_SCB__INTR_SPI_EC_MASK CYREG_SCB1_INTR_SPI_EC_MASK
#define UART_SCB__INTR_SPI_EC_MASKED CYREG_SCB1_INTR_SPI_EC_MASKED
#define UART_SCB__INTR_TX CYREG_SCB1_INTR_TX
#define UART_SCB__INTR_TX_MASK CYREG_SCB1_INTR_TX_MASK
#define UART_SCB__INTR_TX_MASKED CYREG_SCB1_INTR_TX_MASKED
#define UART_SCB__INTR_TX_SET CYREG_SCB1_INTR_TX_SET
#define UART_SCB__RX_CTRL CYREG_SCB1_RX_CTRL
#define UART_SCB__RX_FIFO_CTRL CYREG_SCB1_RX_FIFO_CTRL
#define UART_SCB__RX_FIFO_RD CYREG_SCB1_RX_FIFO_RD
#define UART_SCB__RX_FIFO_RD_SILENT CYREG_SCB1_RX_FIFO_RD_SILENT
#define UART_SCB__RX_FIFO_STATUS CYREG_SCB1_RX_FIFO_STATUS
#define UART_SCB__RX_MATCH CYREG_SCB1_RX_MATCH
#define UART_SCB__SPI_CTRL CYREG_SCB1_SPI_CTRL
#define UART_SCB__SPI_STATUS CYREG_SCB1_SPI_STATUS
#define UART_SCB__SS0_POSISTION 0u
#define UART_SCB__SS1_POSISTION 1u
#define UART_SCB__SS2_POSISTION 2u
#define UART_SCB__SS3_POSISTION 3u
#define UART_SCB__STATUS CYREG_SCB1_STATUS
#define UART_SCB__TX_CTRL CYREG_SCB1_TX_CTRL
#define UART_SCB__TX_FIFO_CTRL CYREG_SCB1_TX_FIFO_CTRL
#define UART_SCB__TX_FIFO_STATUS CYREG_SCB1_TX_FIFO_STATUS
#define UART_SCB__TX_FIFO_WR CYREG_SCB1_TX_FIFO_WR
#define UART_SCB__UART_CTRL CYREG_SCB1_UART_CTRL
#define UART_SCB__UART_FLOW_CTRL CYREG_SCB1_UART_FLOW_CTRL
#define UART_SCB__UART_RX_CTRL CYREG_SCB1_UART_RX_CTRL
#define UART_SCB__UART_RX_STATUS CYREG_SCB1_UART_RX_STATUS
#define UART_SCB__UART_TX_CTRL CYREG_SCB1_UART_TX_CTRL

/* UART_SCBCLK */
#define UART_SCBCLK__CTRL_REGISTER CYREG_PERI_PCLK_CTL1
#define UART_SCBCLK__DIV_ID 0x00000042u
#define UART_SCBCLK__DIV_REGISTER CYREG_PERI_DIV_16_CTL2
#define UART_SCBCLK__PA_DIV_ID 0x000000FFu

/* UART_tx */
#define UART_tx__0__DR CYREG_GPIO_PRT0_DR
#define UART_tx__0__DR_CLR CYREG_GPIO_PRT0_DR_CLR
#define UART_tx__0__DR_INV CYREG_GPIO_PRT0_DR_INV
#define UART_tx__0__DR_SET CYREG_GPIO_PRT0_DR_SET
#define UART_tx__0__HSIOM CYREG_HSIOM_PORT_SEL0
#define UART_tx__0__HSIOM_GPIO 0u
#define UART_tx__0__HSIOM_I2C 14u
#define UART_tx__0__HSIOM_I2C_SDA 14u
#define UART_tx__0__HSIOM_MASK 0x00F00000u
#define UART_tx__0__HSIOM_SHIFT 20u
#define UART_tx__0__HSIOM_SPI 15u
#define UART_tx__0__HSIOM_SPI_MISO 15u
#define UART_tx__0__HSIOM_UART 9u
#define UART_tx__0__HSIOM_UART_TX 9u
#define UART_tx__0__INTCFG CYREG_GPIO_PRT0_INTR_CFG
#define UART_tx__0__INTR CYREG_GPIO_PRT0_INTR
#define UART_tx__0__INTR_CFG CYREG_GPIO_PRT0_INTR_CFG
#define UART_tx__0__INTSTAT CYREG_GPIO_PRT0_INTR
#define UART_tx__0__MASK 0x20u
#define UART_tx__0__PC CYREG_GPIO_PRT0_PC
#define UART_tx__0__PC2 CYREG_GPIO_PRT0_PC2
#define UART_tx__0__PORT 0u
#define UART_tx__0__PS CYREG_GPIO_PRT0_PS
#define UART_tx__0__SHIFT 5u
#define UART_tx__DR CYREG_GPIO_PRT0_DR
#define UART_tx__DR_CLR CYREG_GPIO_PRT0_DR_CLR
#define UART_tx__DR_INV CYREG_GPIO_PRT0_DR_INV
#define UART_tx__DR_SET CYREG_GPIO_PRT0_DR_SET
#define UART_tx__INTCFG CYREG_GPIO_PRT0_INTR_CFG
#define UART_tx__INTR CYREG_GPIO_PRT0_INTR
#define UART_tx__INTR_CFG CYREG_GPIO_PRT0_INTR_CFG
#define UART_tx__INTSTAT CYREG_GPIO_PRT0_INTR
#define UART_tx__MASK 0x20u
#define UART_tx__PC CYREG_GPIO_PRT0_PC
#define UART_tx__PC2 CYREG_GPIO_PRT0_PC2
#define UART_tx__PORT 0u
#define UART_tx__PS CYREG_GPIO_PRT0_PS
#define UART_tx__SHIFT 5u

/* EZI2C_SCB */
#define EZI2C_SCB__CTRL CYREG_SCB2_CTRL
#define EZI2C_SCB__EZ_DATA0 CYREG_SCB2_EZ_DATA0
#define EZI2C_SCB__EZ_DATA1 CYREG_SCB2_EZ_DATA1
#define EZI2C_SCB__EZ_DATA10 CYREG_SCB2_EZ_DATA10
#define EZI2C_SCB__EZ_DATA11 CYREG_SCB2_EZ_DATA11
#define EZI2C_SCB__EZ_DATA12 CYREG_SCB2_EZ_DATA12
#define EZI2C_SCB__EZ_DATA13 CYREG_SCB2_EZ_DATA13
#define EZI2C_SCB__EZ_DATA14 CYREG_SCB2_EZ_DATA14
#define EZI2C_SCB__EZ_DATA15 CYREG_SCB2_EZ_DATA15
#define EZI2C_SCB__EZ_DATA16 CYREG_SCB2_EZ_DATA16
#define EZI2C_SCB__EZ_DATA17 CYREG_SCB2_EZ_DATA17
#define EZI2C_SCB__EZ_DATA18 CYREG_SCB2_EZ_DATA18
#define EZI2C_SCB__EZ_DATA19 CYREG_SCB2_EZ_DATA19
#define EZI2C_SCB__EZ_DATA2 CYREG_SCB2_EZ_DATA2
#define EZI2C_SCB__EZ_DATA20 CYREG_SCB2_EZ_DATA20
#define EZI2C_SCB__EZ_DATA21 CYREG_SCB2_EZ_DATA21
#define EZI2C_SCB__EZ_DATA22 CYREG_SCB2_EZ_DATA22
#define EZI2C_SCB__EZ_DATA23 CYREG_SCB2_EZ_DATA23
#define EZI2C_SCB__EZ_DATA24 CYREG_SCB2_EZ_DATA24
#define EZI2C_SCB__EZ_DATA25 CYREG_SCB2_EZ_DATA25
#define EZI2C_SCB__EZ_DATA26 CYREG_SCB2_EZ_DATA26
#define EZI2C_SCB__EZ_DATA27 CYREG_SCB2_EZ_DATA27
#define EZI2C_SCB__EZ_DATA28 CYREG_SCB2_EZ_DATA28
#define EZI2C_SCB__EZ_DATA29 CYREG_SCB2_EZ_DATA29
#define EZI2C_SCB__EZ_DATA3 CYREG_SCB2_EZ_DATA3
#define EZI2C_SCB__EZ_DATA30 CYREG_SCB2_EZ_DATA30
#define EZI2C_SCB__EZ_DATA31 CYREG_SCB2_EZ_DATA31
#define EZI2C_SCB__EZ_DATA4 CYREG_SCB2_EZ_DATA4
#define EZI2C_SCB__EZ_DATA5 CYREG_SCB2_EZ_DATA5
#define EZI2C_SCB__EZ_DATA6 CYREG_SCB2_EZ_DATA6
#define EZI2C_SCB__EZ_DATA7 CYREG_SCB2_EZ_DATA7
#define EZI2C_SCB__EZ_DATA8 CYREG_SCB2_EZ_DATA8
#define EZI2C_SCB__EZ_DATA9 CYREG_SCB2_EZ_DATA9
#define EZI2C_SCB__I2C_CFG CYREG_SCB2_I2C_CFG
#define EZI2C_SCB__I2C_CTRL CYREG_SCB2_I2C_CTRL
#define EZI2C_SCB__I2C_M_CMD CYREG_SCB2_I2C_M_CMD
#define EZI2C_SCB__I2C_S_CMD CYREG_SCB2_I2C_S_CMD
#define EZI2C_SCB__I2C_STATUS CYREG_SCB2_I2C_STATUS
#define EZI2C_SCB__INTR_CAUSE CYREG_SCB2_INTR_CAUSE
#define EZI2C_SCB__INTR_I2C_EC CYREG_SCB2_INTR_I2C_EC
#define EZI2C_SCB__INTR_I2C_EC_MASK CYREG_SCB2_INTR_I2C_EC_MASK
#define EZI2C_SCB__INTR_I2C_EC_MASKED CYREG_SCB2_INTR_I2C_EC_MASKED
#define EZI2C_SCB__INTR_M CYREG_SCB2_INTR_M
#define EZI2C_SCB__INTR_M_MASK CYREG_SCB2_INTR_M_MASK
#define EZI2C_SCB__INTR_M_MASKED CYREG_SCB2_INTR_M_MASKED
#define EZI2C_SCB__INTR_M_SET CYREG_SCB2_INTR_M_SET
#define EZI2C_SCB__INTR_RX CYREG_SCB2_INTR_RX
#define EZI2C_SCB__INTR_RX_MASK CYREG_SCB2_INTR_RX_MASK
#define EZI2C_SCB__INTR_RX_MASKED CYREG_SCB2_INTR_RX_MASKED
#define EZI2C_SCB__INTR_RX_SET CYREG_SCB2_INTR_RX_SET
#define EZI2C_SCB__INTR_S CYREG_SCB2_INTR_S
#define EZI2C_SCB__INTR_S_MASK CYREG_SCB2_INTR_S_MASK
#define EZI2C_SCB__INTR_S_MASKED CYREG_SCB2_INTR_S_MASKED
#define EZI2C_SCB__INTR_S_SET CYREG_SCB2_INTR_S_SET
#define EZI2C_SCB__INTR_SPI_EC CYREG_SCB2_INTR_SPI_EC
#define EZI2C_SCB__INTR_SPI_EC_MASK CYREG_SCB2_INTR_SPI_EC_MASK
#define EZI2C_SCB__INTR_SPI_EC_MASKED CYREG_SCB2_INTR_SPI_EC_MASKED
#define EZI2C_SCB__INTR_TX CYREG_SCB2_INTR_TX
#define EZI2C_SCB__INTR_TX_MASK CYREG_SCB2_INTR_TX_MASK
#define EZI2C_SCB__INTR_TX_MASKED CYREG_SCB2_INTR_TX_MASKED
#define EZI2C_SCB__INTR_TX_SET CYREG_SCB2_INTR_TX_SET
#define EZI2C_SCB__RX_CTRL CYREG_SCB2_RX_CTRL
#define EZI2C_SCB__RX_FIFO_CTRL CYREG_SCB2_RX_FIFO_CTRL
#define EZI2C_SCB__RX_FIFO_RD CYREG_SCB2_RX_FIFO_RD
#define EZI2C_SCB__RX_FIFO_RD_SILENT CYREG_SCB2_RX_FIFO_RD_SILENT
#define EZI2C_SCB__RX_FIFO_STATUS CYREG_SCB2_RX_FIFO_STATUS
#define EZI2C_SCB__RX_MATCH CYREG_SCB2_RX_MATCH
#define EZI2C_SCB__SPI_CTRL CYREG_SCB2_SPI_CTRL
#define EZI2C_SCB__SPI_STATUS CYREG_SCB2_SPI_STATUS
#define EZI2C_SCB__SS0_POSISTION 0u
#define EZI2C_SCB__SS1_POSISTION 1u
#define EZI2C_SCB__SS2_POSISTION 2u
#define EZI2C_SCB__SS3_POSISTION 3u
#define EZI2C_SCB__STATUS CYREG_SCB2_STATUS
#define EZI2C_SCB__TX_CTRL CYREG_SCB2_TX_CTRL
#define EZI2C_SCB__TX_FIFO_CTRL CYREG_SCB2_TX_FIFO_CTRL
#define EZI2C_SCB__TX_FIFO_STATUS CYREG_SCB2_TX_FIFO_STATUS
#define EZI2C_SCB__TX_FIFO_WR CYREG_SCB2_TX_FIFO_WR
#define EZI2C_SCB__UART_CTRL CYREG_SCB2_UART_CTRL
#define EZI2C_SCB__UART_FLOW_CTRL CYREG_SCB2_UART_FLOW_CTRL
#define EZI2C_SCB__UART_RX_CTRL CYREG_SCB2_UART_RX_CTRL
#define EZI2C_SCB__UART_RX_STATUS CYREG_SCB2_UART_RX_STATUS
#define EZI2C_SCB__UART_TX_CTRL CYREG_SCB2_UART_TX_CTRL

/* EZI2C_SCB_IRQ */
#define EZI2C_SCB_IRQ__INTC_CLR_EN_REG CYREG_CM0P_ICER
#define EZI2C_SCB_IRQ__INTC_CLR_PD_REG CYREG_CM0P_ICPR
#define EZI2C_SCB_IRQ__INTC_MASK 0x200u
#define EZI2C_SCB_IRQ__INTC_NUMBER 9u
#define EZI2C_SCB_IRQ__INTC_PRIOR_MASK 0xC000u
#define EZI2C_SCB_IRQ__INTC_PRIOR_NUM 3u
#define EZI2C_SCB_IRQ__INTC_PRIOR_REG CYREG_CM0P_IPR2
#define EZI2C_SCB_IRQ__INTC_SET_EN_REG CYREG_CM0P_ISER
#define EZI2C_SCB_IRQ__INTC_SET_PD_REG CYREG_CM0P_ISPR

/* EZI2C_SCBCLK */
#define EZI2C_SCBCLK__CTRL_REGISTER CYREG_PERI_PCLK_CTL2
#define EZI2C_SCBCLK__DIV_ID 0x00000040u
#define EZI2C_SCBCLK__DIV_REGISTER CYREG_PERI_DIV_16_CTL0
#define EZI2C_SCBCLK__PA_DIV_ID 0x000000FFu

/* EZI2C_scl */
#define EZI2C_scl__0__DR CYREG_GPIO_PRT0_DR
#define EZI2C_scl__0__DR_CLR CYREG_GPIO_PRT0_DR_CLR
#define EZI2C_scl__0__DR_INV CYREG_GPIO_PRT0_DR_INV
#define EZI2C_scl__0__DR_SET CYREG_GPIO_PRT0_DR_SET
#define EZI2C_scl__0__HSIOM CYREG_HSIOM_PORT_SEL0
#define EZI2C_scl__0__HSIOM_GPIO 0u
#define EZI2C_scl__0__HSIOM_I2C 14u
#define EZI2C_scl__0__HSIOM_I2C_SCL 14u
#define EZI2C_scl__0__HSIOM_MASK 0x0000000Fu
#define EZI2C_scl__0__HSIOM_SHIFT 0u
#define EZI2C_scl__0__HSIOM_UART 9u
#define EZI2C_scl__0__HSIOM_UART_CTS 9u
#define EZI2C_scl__0__INTCFG CYREG_GPIO_PRT0_INTR_CFG
#define EZI2C_scl__0__INTR CYREG_GPIO_PRT0_INTR
#define EZI2C_scl__0__INTR_CFG CYREG_GPIO_PRT0_INTR_CFG
#define EZI2C_scl__0__INTSTAT CYREG_GPIO_PRT0_INTR
#define EZI2C_scl__0__MASK 0x01u
#define EZI2C_scl__0__PC CYREG_GPIO_PRT0_PC
#define EZI2C_scl__0__PC2 CYREG_GPIO_PRT0_PC2
#define EZI2C_scl__0__PORT 0u
#define EZI2C_scl__0__PS CYREG_GPIO_PRT0_PS
#define EZI2C_scl__0__SHIFT 0u
#define EZI2C_scl__DR CYREG_GPIO_PRT0_DR
#define EZI2C_scl__DR_CLR CYREG_GPIO_PRT0_DR_CLR
#define EZI2C_scl__DR_INV CYREG_GPIO_PRT0_DR_INV
#define EZI2C_scl__DR_SET CYREG_GPIO_PRT0_DR_SET
#define EZI2C_scl__INTCFG CYREG_GPIO_PRT0_INTR_CFG
#define EZI2C_scl__INTR CYREG_GPIO_PRT0_INTR
#define EZI2C_scl__INTR_CFG CYREG_GPIO_PRT0_INTR_CFG
#define EZI2C_scl__INTSTAT CYREG_GPIO_PRT0_INTR
#define EZI2C_scl__MASK 0x01u
#define EZI2C_scl__PC CYREG_GPIO_PRT0_PC
#define EZI2C_scl__PC2 CYREG_GPIO_PRT0_PC2
#define EZI2C_scl__PORT 0u
#define EZI2C_scl__PS CYREG_GPIO_PRT0_PS
#define EZI2C_scl__SHIFT 0u

/* EZI2C_sda */
#define EZI2C_sda__0__DR CYREG_GPIO_PRT0_DR
#define EZI2C_sda__0__DR_CLR CYREG_GPIO_PRT0_DR_CLR
#define EZI2C_sda__0__DR_INV CYREG_GPIO_PRT0_DR_INV
#define EZI2C_sda__0__DR_SET CYREG_GPIO_PRT0_DR_SET
#define EZI2C_sda__0__HSIOM CYREG_HSIOM_PORT_SEL0
#define EZI2C_sda__0__HSIOM_GPIO 0u
#define EZI2C_sda__0__HSIOM_I2C 14u
#define EZI2C_sda__0__HSIOM_I2C_SDA 14u
#define EZI2C_sda__0__HSIOM_MASK 0x000000F0u
#define EZI2C_sda__0__HSIOM_SHIFT 4u
#define EZI2C_sda__0__HSIOM_UART 9u
#define EZI2C_sda__0__HSIOM_UART_RTS 9u
#define EZI2C_sda__0__INTCFG CYREG_GPIO_PRT0_INTR_CFG
#define EZI2C_sda__0__INTR CYREG_GPIO_PRT0_INTR
#define EZI2C_sda__0__INTR_CFG CYREG_GPIO_PRT0_INTR_CFG
#define EZI2C_sda__0__INTSTAT CYREG_GPIO_PRT0_INTR
#define EZI2C_sda__0__MASK 0x02u
#define EZI2C_sda__0__PC CYREG_GPIO_PRT0_PC
#define EZI2C_sda__0__PC2 CYREG_GPIO_PRT0_PC2
#define EZI2C_sda__0__PORT 0u
#define EZI2C_sda__0__PS CYREG_GPIO_PRT0_PS
#define EZI2C_sda__0__SHIFT 1u
#define EZI2C_sda__DR CYREG_GPIO_PRT0_DR
#define EZI2C_sda__DR_CLR CYREG_GPIO_PRT0_DR_CLR
#define EZI2C_sda__DR_INV CYREG_GPIO_PRT0_DR_INV
#define EZI2C_sda__DR_SET CYREG_GPIO_PRT0_DR_SET
#define EZI2C_sda__INTCFG CYREG_GPIO_PRT0_INTR_CFG
#define EZI2C_sda__INTR CYREG_GPIO_PRT0_INTR
#define EZI2C_sda__INTR_CFG CYREG_GPIO_PRT0_INTR_CFG
#define EZI2C_sda__INTSTAT CYREG_GPIO_PRT0_INTR
#define EZI2C_sda__MASK 0x02u
#define EZI2C_sda__PC CYREG_GPIO_PRT0_PC
#define EZI2C_sda__PC2 CYREG_GPIO_PRT0_PC2
#define EZI2C_sda__PORT 0u
#define EZI2C_sda__PS CYREG_GPIO_PRT0_PS
#define EZI2C_sda__SHIFT 1u

/* PWM_0_cy_m0s8_tcpwm_1 */
#define PWM_0_cy_m0s8_tcpwm_1__CC CYREG_TCPWM_CNT0_CC
#define PWM_0_cy_m0s8_tcpwm_1__CC_BUFF CYREG_TCPWM_CNT0_CC_BUFF
#define PWM_0_cy_m0s8_tcpwm_1__COUNTER CYREG_TCPWM_CNT0_COUNTER
#define PWM_0_cy_m0s8_tcpwm_1__CTRL CYREG_TCPWM_CNT0_CTRL
#define PWM_0_cy_m0s8_tcpwm_1__INTR CYREG_TCPWM_CNT0_INTR
#define PWM_0_cy_m0s8_tcpwm_1__INTR_MASK CYREG_TCPWM_CNT0_INTR_MASK
#define PWM_0_cy_m0s8_tcpwm_1__INTR_MASKED CYREG_TCPWM_CNT0_INTR_MASKED
#define PWM_0_cy_m0s8_tcpwm_1__INTR_SET CYREG_TCPWM_CNT0_INTR_SET
#define PWM_0_cy_m0s8_tcpwm_1__PERIOD CYREG_TCPWM_CNT0_PERIOD
#define PWM_0_cy_m0s8_tcpwm_1__PERIOD_BUFF CYREG_TCPWM_CNT0_PERIOD_BUFF
#define PWM_0_cy_m0s8_tcpwm_1__STATUS CYREG_TCPWM_CNT0_STATUS
#define PWM_0_cy_m0s8_tcpwm_1__TCPWM_CMD CYREG_TCPWM_CMD
#define PWM_0_cy_m0s8_tcpwm_1__TCPWM_CMDCAPTURE_MASK 0x01u
#define PWM_0_cy_m0s8_tcpwm_1__TCPWM_CMDCAPTURE_SHIFT 0u
#define PWM_0_cy_m0s8_tcpwm_1__TCPWM_CMDRELOAD_MASK 0x100u
#define PWM_0_cy_m0s8_tcpwm_1__TCPWM_CMDRELOAD_SHIFT 8u
#define PWM_0_cy_m0s8_tcpwm_1__TCPWM_CMDSTART_MASK 0x1000000u
#define PWM_0_cy_m0s8_tcpwm_1__TCPWM_CMDSTART_SHIFT 24u
#define PWM_0_cy_m0s8_tcpwm_1__TCPWM_CMDSTOP_MASK 0x10000u
#define PWM_0_cy_m0s8_tcpwm_1__TCPWM_CMDSTOP_SHIFT 16u
#define PWM_0_cy_m0s8_tcpwm_1__TCPWM_CTRL CYREG_TCPWM_CTRL
#define PWM_0_cy_m0s8_tcpwm_1__TCPWM_CTRL_MASK 0x01u
#define PWM_0_cy_m0s8_tcpwm_1__TCPWM_CTRL_SHIFT 0u
#define PWM_0_cy_m0s8_tcpwm_1__TCPWM_INTR_CAUSE CYREG_TCPWM_INTR_CAUSE
#define PWM_0_cy_m0s8_tcpwm_1__TCPWM_INTR_CAUSE_MASK 0x01u
#define PWM_0_cy_m0s8_tcpwm_1__TCPWM_INTR_CAUSE_SHIFT 0u
#define PWM_0_cy_m0s8_tcpwm_1__TCPWM_NUMBER 0u
#define PWM_0_cy_m0s8_tcpwm_1__TR_CTRL0 CYREG_TCPWM_CNT0_TR_CTRL0
#define PWM_0_cy_m0s8_tcpwm_1__TR_CTRL1 CYREG_TCPWM_CNT0_TR_CTRL1
#define PWM_0_cy_m0s8_tcpwm_1__TR_CTRL2 CYREG_TCPWM_CNT0_TR_CTRL2

/* PWM_1_cy_m0s8_tcpwm_1 */
#define PWM_1_cy_m0s8_tcpwm_1__CC CYREG_TCPWM_CNT1_CC
#define PWM_1_cy_m0s8_tcpwm_1__CC_BUFF CYREG_TCPWM_CNT1_CC_BUFF
#define PWM_1_cy_m0s8_tcpwm_1__COUNTER CYREG_TCPWM_CNT1_COUNTER
#define PWM_1_cy_m0s8_tcpwm_1__CTRL CYREG_TCPWM_CNT1_CTRL
#define PWM_1_cy_m0s8_tcpwm_1__INTR CYREG_TCPWM_CNT1_INTR
#define PWM_1_cy_m0s8_tcpwm_1__INTR_MASK CYREG_TCPWM_CNT1_INTR_MASK
#define PWM_1_cy_m0s8_tcpwm_1__INTR_MASKED CYREG_TCPWM_CNT1_INTR_MASKED
#define PWM_1_cy_m0s8_tcpwm_1__INTR_SET CYREG_TCPWM_CNT1_INTR_SET
#define PWM_1_cy_m0s8_tcpwm_1__PERIOD CYREG_TCPWM_CNT1_PERIOD
#define PWM_1_cy_m0s8_tcpwm_1__PERIOD_BUFF CYREG_TCPWM_CNT1_PERIOD_BUFF
#define PWM_1_cy_m0s8_tcpwm_1__STATUS CYREG_TCPWM_CNT1_STATUS
#define PWM_1_cy_m0s8_tcpwm_1__TCPWM_CMD CYREG_TCPWM_CMD
#define PWM_1_cy_m0s8_tcpwm_1__TCPWM_CMDCAPTURE_MASK 0x02u
#define PWM_1_cy_m0s8_tcpwm_1__TCPWM_CMDCAPTURE_SHIFT 1u
#define PWM_1_cy_m0s8_tcpwm_1__TCPWM_CMDRELOAD_MASK 0x200u
#define PWM_1_cy_m0s8_tcpwm_1__TCPWM_CMDRELOAD_SHIFT 9u
#define PWM_1_cy_m0s8_tcpwm_1__TCPWM_CMDSTART_MASK 0x2000000u
#define PWM_1_cy_m0s8_tcpwm_1__TCPWM_CMDSTART_SHIFT 25u
#define PWM_1_cy_m0s8_tcpwm_1__TCPWM_CMDSTOP_MASK 0x20000u
#define PWM_1_cy_m0s8_tcpwm_1__TCPWM_CMDSTOP_SHIFT 17u
#define PWM_1_cy_m0s8_tcpwm_1__TCPWM_CTRL CYREG_TCPWM_CTRL
#define PWM_1_cy_m0s8_tcpwm_1__TCPWM_CTRL_MASK 0x02u
#define PWM_1_cy_m0s8_tcpwm_1__TCPWM_CTRL_SHIFT 1u
#define PWM_1_cy_m0s8_tcpwm_1__TCPWM_INTR_CAUSE CYREG_TCPWM_INTR_CAUSE
#define PWM_1_cy_m0s8_tcpwm_1__TCPWM_INTR_CAUSE_MASK 0x02u
#define PWM_1_cy_m0s8_tcpwm_1__TCPWM_INTR_CAUSE_SHIFT 1u
#define PWM_1_cy_m0s8_tcpwm_1__TCPWM_NUMBER 1u
#define PWM_1_cy_m0s8_tcpwm_1__TR_CTRL0 CYREG_TCPWM_CNT1_TR_CTRL0
#define PWM_1_cy_m0s8_tcpwm_1__TR_CTRL1 CYREG_TCPWM_CNT1_TR_CTRL1
#define PWM_1_cy_m0s8_tcpwm_1__TR_CTRL2 CYREG_TCPWM_CNT1_TR_CTRL2

/* PWM_2_cy_m0s8_tcpwm_1 */
#define PWM_2_cy_m0s8_tcpwm_1__CC CYREG_TCPWM_CNT2_CC
#define PWM_2_cy_m0s8_tcpwm_1__CC_BUFF CYREG_TCPWM_CNT2_CC_BUFF
#define PWM_2_cy_m0s8_tcpwm_1__COUNTER CYREG_TCPWM_CNT2_COUNTER
#define PWM_2_cy_m0s8_tcpwm_1__CTRL CYREG_TCPWM_CNT2_CTRL
#define PWM_2_cy_m0s8_tcpwm_1__INTR CYREG_TCPWM_CNT2_INTR
#define PWM_2_cy_m0s8_tcpwm_1__INTR_MASK CYREG_TCPWM_CNT2_INTR_MASK
#define PWM_2_cy_m0s8_tcpwm_1__INTR_MASKED CYREG_TCPWM_CNT2_INTR_MASKED
#define PWM_2_cy_m0s8_tcpwm_1__INTR_SET CYREG_TCPWM_CNT2_INTR_SET
#define PWM_2_cy_m0s8_tcpwm_1__PERIOD CYREG_TCPWM_CNT2_PERIOD
#define PWM_2_cy_m0s8_tcpwm_1__PERIOD_BUFF CYREG_TCPWM_CNT2_PERIOD_BUFF
#define PWM_2_cy_m0s8_tcpwm_1__STATUS CYREG_TCPWM_CNT2_STATUS
#define PWM_2_cy_m0s8_tcpwm_1__TCPWM_CMD CYREG_TCPWM_CMD
#define PWM_2_cy_m0s8_tcpwm_1__TCPWM_CMDCAPTURE_MASK 0x04u
#define PWM_2_cy_m0s8_tcpwm_1__TCPWM_CMDCAPTURE_SHIFT 2u
#define PWM_2_cy_m0s8_tcpwm_1__TCPWM_CMDRELOAD_MASK 0x400u
#define PWM_2_cy_m0s8_tcpwm_1__TCPWM_CMDRELOAD_SHIFT 10u
#define PWM_2_cy_m0s8_tcpwm_1__TCPWM_CMDSTART_MASK 0x4000000u
#define PWM_2_cy_m0s8_tcpwm_1__TCPWM_CMDSTART_SHIFT 26u
#define PWM_2_cy_m0s8_tcpwm_1__TCPWM_CMDSTOP_MASK 0x40000u
#define PWM_2_cy_m0s8_tcpwm_1__TCPWM_CMDSTOP_SHIFT 18u
#define PWM_2_cy_m0s8_tcpwm_1__TCPWM_CTRL CYREG_TCPWM_CTRL
#define PWM_2_cy_m0s8_tcpwm_1__TCPWM_CTRL_MASK 0x04u
#define PWM_2_cy_m0s8_tcpwm_1__TCPWM_CTRL_SHIFT 2u
#define PWM_2_cy_m0s8_tcpwm_1__TCPWM_INTR_CAUSE CYREG_TCPWM_INTR_CAUSE
#define PWM_2_cy_m0s8_tcpwm_1__TCPWM_INTR_CAUSE_MASK 0x04u
#define PWM_2_cy_m0s8_tcpwm_1__TCPWM_INTR_CAUSE_SHIFT 2u
#define PWM_2_cy_m0s8_tcpwm_1__TCPWM_NUMBER 2u
#define PWM_2_cy_m0s8_tcpwm_1__TR_CTRL0 CYREG_TCPWM_CNT2_TR_CTRL0
#define PWM_2_cy_m0s8_tcpwm_1__TR_CTRL1 CYREG_TCPWM_CNT2_TR_CTRL1
#define PWM_2_cy_m0s8_tcpwm_1__TR_CTRL2 CYREG_TCPWM_CNT2_TR_CTRL2

/* PWM_3_cy_m0s8_tcpwm_1 */
#define PWM_3_cy_m0s8_tcpwm_1__CC CYREG_TCPWM_CNT3_CC
#define PWM_3_cy_m0s8_tcpwm_1__CC_BUFF CYREG_TCPWM_CNT3_CC_BUFF
#define PWM_3_cy_m0s8_tcpwm_1__COUNTER CYREG_TCPWM_CNT3_COUNTER
#define PWM_3_cy_m0s8_tcpwm_1__CTRL CYREG_TCPWM_CNT3_CTRL
#define PWM_3_cy_m0s8_tcpwm_1__INTR CYREG_TCPWM_CNT3_INTR
#define PWM_3_cy_m0s8_tcpwm_1__INTR_MASK CYREG_TCPWM_CNT3_INTR_MASK
#define PWM_3_cy_m0s8_tcpwm_1__INTR_MASKED CYREG_TCPWM_CNT3_INTR_MASKED
#define PWM_3_cy_m0s8_tcpwm_1__INTR_SET CYREG_TCPWM_CNT3_INTR_SET
#define PWM_3_cy_m0s8_tcpwm_1__PERIOD CYREG_TCPWM_CNT3_PERIOD
#define PWM_3_cy_m0s8_tcpwm_1__PERIOD_BUFF CYREG_TCPWM_CNT3_PERIOD_BUFF
#define PWM_3_cy_m0s8_tcpwm_1__STATUS CYREG_TCPWM_CNT3_STATUS
#define PWM_3_cy_m0s8_tcpwm_1__TCPWM_CMD CYREG_TCPWM_CMD
#define PWM_3_cy_m0s8_tcpwm_1__TCPWM_CMDCAPTURE_MASK 0x08u
#define PWM_3_cy_m0s8_tcpwm_1__TCPWM_CMDCAPTURE_SHIFT 3u
#define PWM_3_cy_m0s8_tcpwm_1__TCPWM_CMDRELOAD_MASK 0x800u
#define PWM_3_cy_m0s8_tcpwm_1__TCPWM_CMDRELOAD_SHIFT 11u
#define PWM_3_cy_m0s8_tcpwm_1__TCPWM_CMDSTART_MASK 0x8000000u
#define PWM_3_cy_m0s8_tcpwm_1__TCPWM_CMDSTART_SHIFT 27u
#define PWM_3_cy_m0s8_tcpwm_1__TCPWM_CMDSTOP_MASK 0x80000u
#define PWM_3_cy_m0s8_tcpwm_1__TCPWM_CMDSTOP_SHIFT 19u
#define PWM_3_cy_m0s8_tcpwm_1__TCPWM_CTRL CYREG_TCPWM_CTRL
#define PWM_3_cy_m0s8_tcpwm_1__TCPWM_CTRL_MASK 0x08u
#define PWM_3_cy_m0s8_tcpwm_1__TCPWM_CTRL_SHIFT 3u
#define PWM_3_cy_m0s8_tcpwm_1__TCPWM_INTR_CAUSE CYREG_TCPWM_INTR_CAUSE
#define PWM_3_cy_m0s8_tcpwm_1__TCPWM_INTR_CAUSE_MASK 0x08u
#define PWM_3_cy_m0s8_tcpwm_1__TCPWM_INTR_CAUSE_SHIFT 3u
#define PWM_3_cy_m0s8_tcpwm_1__TCPWM_NUMBER 3u
#define PWM_3_cy_m0s8_tcpwm_1__TR_CTRL0 CYREG_TCPWM_CNT3_TR_CTRL0
#define PWM_3_cy_m0s8_tcpwm_1__TR_CTRL1 CYREG_TCPWM_CNT3_TR_CTRL1
#define PWM_3_cy_m0s8_tcpwm_1__TR_CTRL2 CYREG_TCPWM_CNT3_TR_CTRL2

/* PWM_4_cy_m0s8_tcpwm_1 */
#define PWM_4_cy_m0s8_tcpwm_1__CC CYREG_TCPWM_CNT4_CC
#define PWM_4_cy_m0s8_tcpwm_1__CC_BUFF CYREG_TCPWM_CNT4_CC_BUFF
#define PWM_4_cy_m0s8_tcpwm_1__COUNTER CYREG_TCPWM_CNT4_COUNTER
#define PWM_4_cy_m0s8_tcpwm_1__CTRL CYREG_TCPWM_CNT4_CTRL
#define PWM_4_cy_m0s8_tcpwm_1__INTR CYREG_TCPWM_CNT4_INTR
#define PWM_4_cy_m0s8_tcpwm_1__INTR_MASK CYREG_TCPWM_CNT4_INTR_MASK
#define PWM_4_cy_m0s8_tcpwm_1__INTR_MASKED CYREG_TCPWM_CNT4_INTR_MASKED
#define PWM_4_cy_m0s8_tcpwm_1__INTR_SET CYREG_TCPWM_CNT4_INTR_SET
#define PWM_4_cy_m0s8_tcpwm_1__PERIOD CYREG_TCPWM_CNT4_PERIOD
#define PWM_4_cy_m0s8_tcpwm_1__PERIOD_BUFF CYREG_TCPWM_CNT4_PERIOD_BUFF
#define PWM_4_cy_m0s8_tcpwm_1__STATUS CYREG_TCPWM_CNT4_STATUS
#define PWM_4_cy_m0s8_tcpwm_1__TCPWM_CMD CYREG_TCPWM_CMD
#define PWM_4_cy_m0s8_tcpwm_1__TCPWM_CMDCAPTURE_MASK 0x10u
#define PWM_4_cy_m0s8_tcpwm_1__TCPWM_CMDCAPTURE_SHIFT 4u
#define PWM_4_cy_m0s8_tcpwm_1__TCPWM_CMDRELOAD_MASK 0x1000u
#define PWM_4_cy_m0s8_tcpwm_1__TCPWM_CMDRELOAD_SHIFT 12u
#define PWM_4_cy_m0s8_tcpwm_1__TCPWM_CMDSTART_MASK 0x10000000u
#define PWM_4_cy_m0s8_tcpwm_1__TCPWM_CMDSTART_SHIFT 28u
#define PWM_4_cy_m0s8_tcpwm_1__TCPWM_CMDSTOP_MASK 0x100000u
#define PWM_4_cy_m0s8_tcpwm_1__TCPWM_CMDSTOP_SHIFT 20u
#define PWM_4_cy_m0s8_tcpwm_1__TCPWM_CTRL CYREG_TCPWM_CTRL
#define PWM_4_cy_m0s8_tcpwm_1__TCPWM_CTRL_MASK 0x10u
#define PWM_4_cy_m0s8_tcpwm_1__TCPWM_CTRL_SHIFT 4u
#define PWM_4_cy_m0s8_tcpwm_1__TCPWM_INTR_CAUSE CYREG_TCPWM_INTR_CAUSE
#define PWM_4_cy_m0s8_tcpwm_1__TCPWM_INTR_CAUSE_MASK 0x10u
#define PWM_4_cy_m0s8_tcpwm_1__TCPWM_INTR_CAUSE_SHIFT 4u
#define PWM_4_cy_m0s8_tcpwm_1__TCPWM_NUMBER 4u
#define PWM_4_cy_m0s8_tcpwm_1__TR_CTRL0 CYREG_TCPWM_CNT4_TR_CTRL0
#define PWM_4_cy_m0s8_tcpwm_1__TR_CTRL1 CYREG_TCPWM_CNT4_TR_CTRL1
#define PWM_4_cy_m0s8_tcpwm_1__TR_CTRL2 CYREG_TCPWM_CNT4_TR_CTRL2

/* Clock_1 */
#define Clock_1__CTRL_REGISTER CYREG_PERI_PCLK_CTL8
#define Clock_1__DIV_ID 0x00000041u
#define Clock_1__DIV_REGISTER CYREG_PERI_DIV_16_CTL1
#define Clock_1__PA_DIV_ID 0x000000FFu

/* Servo_0 */
#define Servo_0__0__DR CYREG_GPIO_PRT3_DR
#define Servo_0__0__DR_CLR CYREG_GPIO_PRT3_DR_CLR
#define Servo_0__0__DR_INV CYREG_GPIO_PRT3_DR_INV
#define Servo_0__0__DR_SET CYREG_GPIO_PRT3_DR_SET
#define Servo_0__0__HSIOM CYREG_HSIOM_PORT_SEL3
#define Servo_0__0__HSIOM_MASK 0x0000000Fu
#define Servo_0__0__HSIOM_SHIFT 0u
#define Servo_0__0__INTCFG CYREG_GPIO_PRT3_INTR_CFG
#define Servo_0__0__INTR CYREG_GPIO_PRT3_INTR
#define Servo_0__0__INTR_CFG CYREG_GPIO_PRT3_INTR_CFG
#define Servo_0__0__INTSTAT CYREG_GPIO_PRT3_INTR
#define Servo_0__0__MASK 0x01u
#define Servo_0__0__PC CYREG_GPIO_PRT3_PC
#define Servo_0__0__PC2 CYREG_GPIO_PRT3_PC2
#define Servo_0__0__PORT 3u
#define Servo_0__0__PS CYREG_GPIO_PRT3_PS
#define Servo_0__0__SHIFT 0u
#define Servo_0__DR CYREG_GPIO_PRT3_DR
#define Servo_0__DR_CLR CYREG_GPIO_PRT3_DR_CLR
#define Servo_0__DR_INV CYREG_GPIO_PRT3_DR_INV
#define Servo_0__DR_SET CYREG_GPIO_PRT3_DR_SET
#define Servo_0__INTCFG CYREG_GPIO_PRT3_INTR_CFG
#define Servo_0__INTR CYREG_GPIO_PRT3_INTR
#define Servo_0__INTR_CFG CYREG_GPIO_PRT3_INTR_CFG
#define Servo_0__INTSTAT CYREG_GPIO_PRT3_INTR
#define Servo_0__MASK 0x01u
#define Servo_0__PC CYREG_GPIO_PRT3_PC
#define Servo_0__PC2 CYREG_GPIO_PRT3_PC2
#define Servo_0__PORT 3u
#define Servo_0__PS CYREG_GPIO_PRT3_PS
#define Servo_0__SHIFT 0u

/* Servo_1 */
#define Servo_1__0__DR CYREG_GPIO_PRT2_DR
#define Servo_1__0__DR_CLR CYREG_GPIO_PRT2_DR_CLR
#define Servo_1__0__DR_INV CYREG_GPIO_PRT2_DR_INV
#define Servo_1__0__DR_SET CYREG_GPIO_PRT2_DR_SET
#define Servo_1__0__HSIOM CYREG_HSIOM_PORT_SEL2
#define Servo_1__0__HSIOM_MASK 0x0F000000u
#define Servo_1__0__HSIOM_SHIFT 24u
#define Servo_1__0__INTCFG CYREG_GPIO_PRT2_INTR_CFG
#define Servo_1__0__INTR CYREG_GPIO_PRT2_INTR
#define Servo_1__0__INTR_CFG CYREG_GPIO_PRT2_INTR_CFG
#define Servo_1__0__INTSTAT CYREG_GPIO_PRT2_INTR
#define Servo_1__0__MASK 0x40u
#define Servo_1__0__PC CYREG_GPIO_PRT2_PC
#define Servo_1__0__PC2 CYREG_GPIO_PRT2_PC2
#define Servo_1__0__PORT 2u
#define Servo_1__0__PS CYREG_GPIO_PRT2_PS
#define Servo_1__0__SHIFT 6u
#define Servo_1__DR CYREG_GPIO_PRT2_DR
#define Servo_1__DR_CLR CYREG_GPIO_PRT2_DR_CLR
#define Servo_1__DR_INV CYREG_GPIO_PRT2_DR_INV
#define Servo_1__DR_SET CYREG_GPIO_PRT2_DR_SET
#define Servo_1__INTCFG CYREG_GPIO_PRT2_INTR_CFG
#define Servo_1__INTR CYREG_GPIO_PRT2_INTR
#define Servo_1__INTR_CFG CYREG_GPIO_PRT2_INTR_CFG
#define Servo_1__INTSTAT CYREG_GPIO_PRT2_INTR
#define Servo_1__MASK 0x40u
#define Servo_1__PC CYREG_GPIO_PRT2_PC
#define Servo_1__PC2 CYREG_GPIO_PRT2_PC2
#define Servo_1__PORT 2u
#define Servo_1__PS CYREG_GPIO_PRT2_PS
#define Servo_1__SHIFT 6u

/* Servo_2 */
#define Servo_2__0__DR CYREG_GPIO_PRT1_DR
#define Servo_2__0__DR_CLR CYREG_GPIO_PRT1_DR_CLR
#define Servo_2__0__DR_INV CYREG_GPIO_PRT1_DR_INV
#define Servo_2__0__DR_SET CYREG_GPIO_PRT1_DR_SET
#define Servo_2__0__HSIOM CYREG_HSIOM_PORT_SEL1
#define Servo_2__0__HSIOM_MASK 0x0000000Fu
#define Servo_2__0__HSIOM_SHIFT 0u
#define Servo_2__0__INTCFG CYREG_GPIO_PRT1_INTR_CFG
#define Servo_2__0__INTR CYREG_GPIO_PRT1_INTR
#define Servo_2__0__INTR_CFG CYREG_GPIO_PRT1_INTR_CFG
#define Servo_2__0__INTSTAT CYREG_GPIO_PRT1_INTR
#define Servo_2__0__MASK 0x01u
#define Servo_2__0__PC CYREG_GPIO_PRT1_PC
#define Servo_2__0__PC2 CYREG_GPIO_PRT1_PC2
#define Servo_2__0__PORT 1u
#define Servo_2__0__PS CYREG_GPIO_PRT1_PS
#define Servo_2__0__SHIFT 0u
#define Servo_2__DR CYREG_GPIO_PRT1_DR
#define Servo_2__DR_CLR CYREG_GPIO_PRT1_DR_CLR
#define Servo_2__DR_INV CYREG_GPIO_PRT1_DR_INV
#define Servo_2__DR_SET CYREG_GPIO_PRT1_DR_SET
#define Servo_2__INTCFG CYREG_GPIO_PRT1_INTR_CFG
#define Servo_2__INTR CYREG_GPIO_PRT1_INTR
#define Servo_2__INTR_CFG CYREG_GPIO_PRT1_INTR_CFG
#define Servo_2__INTSTAT CYREG_GPIO_PRT1_INTR
#define Servo_2__MASK 0x01u
#define Servo_2__PC CYREG_GPIO_PRT1_PC
#define Servo_2__PC2 CYREG_GPIO_PRT1_PC2
#define Servo_2__PORT 1u
#define Servo_2__PS CYREG_GPIO_PRT1_PS
#define Servo_2__SHIFT 0u

/* Servo_3 */
#define Servo_3__0__DR CYREG_GPIO_PRT1_DR
#define Servo_3__0__DR_CLR CYREG_GPIO_PRT1_DR_CLR
#define Servo_3__0__DR_INV CYREG_GPIO_PRT1_DR_INV
#define Servo_3__0__DR_SET CYREG_GPIO_PRT1_DR_SET
#define Servo_3__0__HSIOM CYREG_HSIOM_PORT_SEL1
#define Servo_3__0__HSIOM_MASK 0x00000F00u
#define Servo_3__0__HSIOM_SHIFT 8u
#define Servo_3__0__INTCFG CYREG_GPIO_PRT1_INTR_CFG
#define Servo_3__0__INTR CYREG_GPIO_PRT1_INTR
#define Servo_3__0__INTR_CFG CYREG_GPIO_PRT1_INTR_CFG
#define Servo_3__0__INTSTAT CYREG_GPIO_PRT1_INTR
#define Servo_3__0__MASK 0x04u
#define Servo_3__0__PC CYREG_GPIO_PRT1_PC
#define Servo_3__0__PC2 CYREG_GPIO_PRT1_PC2
#define Servo_3__0__PORT 1u
#define Servo_3__0__PS CYREG_GPIO_PRT1_PS
#define Servo_3__0__SHIFT 2u
#define Servo_3__DR CYREG_GPIO_PRT1_DR
#define Servo_3__DR_CLR CYREG_GPIO_PRT1_DR_CLR
#define Servo_3__DR_INV CYREG_GPIO_PRT1_DR_INV
#define Servo_3__DR_SET CYREG_GPIO_PRT1_DR_SET
#define Servo_3__INTCFG CYREG_GPIO_PRT1_INTR_CFG
#define Servo_3__INTR CYREG_GPIO_PRT1_INTR
#define Servo_3__INTR_CFG CYREG_GPIO_PRT1_INTR_CFG
#define Servo_3__INTSTAT CYREG_GPIO_PRT1_INTR
#define Servo_3__MASK 0x04u
#define Servo_3__PC CYREG_GPIO_PRT1_PC
#define Servo_3__PC2 CYREG_GPIO_PRT1_PC2
#define Servo_3__PORT 1u
#define Servo_3__PS CYREG_GPIO_PRT1_PS
#define Servo_3__SHIFT 2u

/* Servo_4 */
#define Servo_4__0__DR CYREG_GPIO_PRT2_DR
#define Servo_4__0__DR_CLR CYREG_GPIO_PRT2_DR_CLR
#define Servo_4__0__DR_INV CYREG_GPIO_PRT2_DR_INV
#define Servo_4__0__DR_SET CYREG_GPIO_PRT2_DR_SET
#define Servo_4__0__HSIOM CYREG_HSIOM_PORT_SEL2
#define Servo_4__0__HSIOM_MASK 0x0000000Fu
#define Servo_4__0__HSIOM_SHIFT 0u
#define Servo_4__0__INTCFG CYREG_GPIO_PRT2_INTR_CFG
#define Servo_4__0__INTR CYREG_GPIO_PRT2_INTR
#define Servo_4__0__INTR_CFG CYREG_GPIO_PRT2_INTR_CFG
#define Servo_4__0__INTSTAT CYREG_GPIO_PRT2_INTR
#define Servo_4__0__MASK 0x01u
#define Servo_4__0__PC CYREG_GPIO_PRT2_PC
#define Servo_4__0__PC2 CYREG_GPIO_PRT2_PC2
#define Servo_4__0__PORT 2u
#define Servo_4__0__PS CYREG_GPIO_PRT2_PS
#define Servo_4__0__SHIFT 0u
#define Servo_4__DR CYREG_GPIO_PRT2_DR
#define Servo_4__DR_CLR CYREG_GPIO_PRT2_DR_CLR
#define Servo_4__DR_INV CYREG_GPIO_PRT2_DR_INV
#define Servo_4__DR_SET CYREG_GPIO_PRT2_DR_SET
#define Servo_4__INTCFG CYREG_GPIO_PRT2_INTR_CFG
#define Servo_4__INTR CYREG_GPIO_PRT2_INTR
#define Servo_4__INTR_CFG CYREG_GPIO_PRT2_INTR_CFG
#define Servo_4__INTSTAT CYREG_GPIO_PRT2_INTR
#define Servo_4__MASK 0x01u
#define Servo_4__PC CYREG_GPIO_PRT2_PC
#define Servo_4__PC2 CYREG_GPIO_PRT2_PC2
#define Servo_4__PORT 2u
#define Servo_4__PS CYREG_GPIO_PRT2_PS
#define Servo_4__SHIFT 0u

/* I2C_OUT_EN */
#define I2C_OUT_EN__0__DR CYREG_GPIO_PRT2_DR
#define I2C_OUT_EN__0__DR_CLR CYREG_GPIO_PRT2_DR_CLR
#define I2C_OUT_EN__0__DR_INV CYREG_GPIO_PRT2_DR_INV
#define I2C_OUT_EN__0__DR_SET CYREG_GPIO_PRT2_DR_SET
#define I2C_OUT_EN__0__HSIOM CYREG_HSIOM_PORT_SEL2
#define I2C_OUT_EN__0__HSIOM_MASK 0x00000F00u
#define I2C_OUT_EN__0__HSIOM_SHIFT 8u
#define I2C_OUT_EN__0__INTCFG CYREG_GPIO_PRT2_INTR_CFG
#define I2C_OUT_EN__0__INTR CYREG_GPIO_PRT2_INTR
#define I2C_OUT_EN__0__INTR_CFG CYREG_GPIO_PRT2_INTR_CFG
#define I2C_OUT_EN__0__INTSTAT CYREG_GPIO_PRT2_INTR
#define I2C_OUT_EN__0__MASK 0x04u
#define I2C_OUT_EN__0__PC CYREG_GPIO_PRT2_PC
#define I2C_OUT_EN__0__PC2 CYREG_GPIO_PRT2_PC2
#define I2C_OUT_EN__0__PORT 2u
#define I2C_OUT_EN__0__PS CYREG_GPIO_PRT2_PS
#define I2C_OUT_EN__0__SHIFT 2u
#define I2C_OUT_EN__DR CYREG_GPIO_PRT2_DR
#define I2C_OUT_EN__DR_CLR CYREG_GPIO_PRT2_DR_CLR
#define I2C_OUT_EN__DR_INV CYREG_GPIO_PRT2_DR_INV
#define I2C_OUT_EN__DR_SET CYREG_GPIO_PRT2_DR_SET
#define I2C_OUT_EN__INTCFG CYREG_GPIO_PRT2_INTR_CFG
#define I2C_OUT_EN__INTR CYREG_GPIO_PRT2_INTR
#define I2C_OUT_EN__INTR_CFG CYREG_GPIO_PRT2_INTR_CFG
#define I2C_OUT_EN__INTSTAT CYREG_GPIO_PRT2_INTR
#define I2C_OUT_EN__MASK 0x04u
#define I2C_OUT_EN__PC CYREG_GPIO_PRT2_PC
#define I2C_OUT_EN__PC2 CYREG_GPIO_PRT2_PC2
#define I2C_OUT_EN__PORT 2u
#define I2C_OUT_EN__PS CYREG_GPIO_PRT2_PS
#define I2C_OUT_EN__SHIFT 2u

/* Miscellaneous */
#define CY_PROJECT_NAME "Spectacle_Servo_Control_Board"
#define CY_VERSION "PSoC Creator  4.0 Update 1"
#define CYDEV_BANDGAP_VOLTAGE 1.200
#define CYDEV_BCLK__HFCLK__HZ 48000000U
#define CYDEV_BCLK__HFCLK__KHZ 48000U
#define CYDEV_BCLK__HFCLK__MHZ 48U
#define CYDEV_BCLK__SYSCLK__HZ 48000000U
#define CYDEV_BCLK__SYSCLK__KHZ 48000U
#define CYDEV_BCLK__SYSCLK__MHZ 48U
#define CYDEV_CHIP_DIE_LEOPARD 1u
#define CYDEV_CHIP_DIE_PSOC4A 12u
#define CYDEV_CHIP_DIE_PSOC5LP 19u
#define CYDEV_CHIP_DIE_PSOC5TM 20u
#define CYDEV_CHIP_DIE_TMA4 2u
#define CYDEV_CHIP_DIE_UNKNOWN 0u
#define CYDEV_CHIP_FAMILY_FM0P 4u
#define CYDEV_CHIP_FAMILY_FM3 5u
#define CYDEV_CHIP_FAMILY_FM4 6u
#define CYDEV_CHIP_FAMILY_PSOC3 1u
#define CYDEV_CHIP_FAMILY_PSOC4 2u
#define CYDEV_CHIP_FAMILY_PSOC5 3u
#define CYDEV_CHIP_FAMILY_UNKNOWN 0u
#define CYDEV_CHIP_FAMILY_USED CYDEV_CHIP_FAMILY_PSOC4
#define CYDEV_CHIP_JTAG_ID 0x1B0E11ABu
#define CYDEV_CHIP_MEMBER_3A 1u
#define CYDEV_CHIP_MEMBER_4A 12u
#define CYDEV_CHIP_MEMBER_4C 18u
#define CYDEV_CHIP_MEMBER_4D 8u
#define CYDEV_CHIP_MEMBER_4E 4u
#define CYDEV_CHIP_MEMBER_4F 13u
#define CYDEV_CHIP_MEMBER_4G 2u
#define CYDEV_CHIP_MEMBER_4H 11u
#define CYDEV_CHIP_MEMBER_4I 17u
#define CYDEV_CHIP_MEMBER_4J 9u
#define CYDEV_CHIP_MEMBER_4K 10u
#define CYDEV_CHIP_MEMBER_4L 16u
#define CYDEV_CHIP_MEMBER_4M 15u
#define CYDEV_CHIP_MEMBER_4N 6u
#define CYDEV_CHIP_MEMBER_4O 5u
#define CYDEV_CHIP_MEMBER_4P 14u
#define CYDEV_CHIP_MEMBER_4Q 7u
#define CYDEV_CHIP_MEMBER_4U 3u
#define CYDEV_CHIP_MEMBER_5A 20u
#define CYDEV_CHIP_MEMBER_5B 19u
#define CYDEV_CHIP_MEMBER_FM3 24u
#define CYDEV_CHIP_MEMBER_FM4 25u
#define CYDEV_CHIP_MEMBER_PDL_FM0P_TYPE1 21u
#define CYDEV_CHIP_MEMBER_PDL_FM0P_TYPE2 22u
#define CYDEV_CHIP_MEMBER_PDL_FM0P_TYPE3 23u
#define CYDEV_CHIP_MEMBER_UNKNOWN 0u
#define CYDEV_CHIP_MEMBER_USED CYDEV_CHIP_MEMBER_4K
#define CYDEV_CHIP_DIE_EXPECT CYDEV_CHIP_MEMBER_USED
#define CYDEV_CHIP_DIE_ACTUAL CYDEV_CHIP_DIE_EXPECT
#define CYDEV_CHIP_REV_LEOPARD_ES1 0u
#define CYDEV_CHIP_REV_LEOPARD_ES2 1u
#define CYDEV_CHIP_REV_LEOPARD_ES3 3u
#define CYDEV_CHIP_REV_LEOPARD_PRODUCTION 3u
#define CYDEV_CHIP_REV_PSOC4A_ES0 17u
#define CYDEV_CHIP_REV_PSOC4A_PRODUCTION 17u
#define CYDEV_CHIP_REV_PSOC5LP_ES0 0u
#define CYDEV_CHIP_REV_PSOC5LP_PRODUCTION 0u
#define CYDEV_CHIP_REV_PSOC5TM_ES0 0u
#define CYDEV_CHIP_REV_PSOC5TM_ES1 1u
#define CYDEV_CHIP_REV_PSOC5TM_PRODUCTION 1u
#define CYDEV_CHIP_REV_TMA4_ES 17u
#define CYDEV_CHIP_REV_TMA4_ES2 33u
#define CYDEV_CHIP_REV_TMA4_PRODUCTION 17u
#define CYDEV_CHIP_REVISION_3A_ES1 0u
#define CYDEV_CHIP_REVISION_3A_ES2 1u
#define CYDEV_CHIP_REVISION_3A_ES3 3u
#define CYDEV_CHIP_REVISION_3A_PRODUCTION 3u
#define CYDEV_CHIP_REVISION_4A_ES0 17u
#define CYDEV_CHIP_REVISION_4A_PRODUCTION 17u
#define CYDEV_CHIP_REVISION_4C_PRODUCTION 0u
#define CYDEV_CHIP_REVISION_4D_PRODUCTION 0u
#define CYDEV_CHIP_REVISION_4E_PRODUCTION 0u
#define CYDEV_CHIP_REVISION_4F_PRODUCTION 0u
#define CYDEV_CHIP_REVISION_4F_PRODUCTION_256DMA 0u
#define CYDEV_CHIP_REVISION_4F_PRODUCTION_256K 0u
#define CYDEV_CHIP_REVISION_4G_ES 17u
#define CYDEV_CHIP_REVISION_4G_ES2 33u
#define CYDEV_CHIP_REVISION_4G_PRODUCTION 17u
#define CYDEV_CHIP_REVISION_4H_PRODUCTION 0u
#define CYDEV_CHIP_REVISION_4I_PRODUCTION 0u
#define CYDEV_CHIP_REVISION_4J_PRODUCTION 0u
#define CYDEV_CHIP_REVISION_4K_PRODUCTION 0u
#define CYDEV_CHIP_REVISION_4L_PRODUCTION 0u
#define CYDEV_CHIP_REVISION_4M_PRODUCTION 0u
#define CYDEV_CHIP_REVISION_4N_PRODUCTION 0u
#define CYDEV_CHIP_REVISION_4O_PRODUCTION 0u
#define CYDEV_CHIP_REVISION_4P_PRODUCTION 0u
#define CYDEV_CHIP_REVISION_4Q_PRODUCTION 0u
#define CYDEV_CHIP_REVISION_4U_PRODUCTION 0u
#define CYDEV_CHIP_REVISION_5A_ES0 0u
#define CYDEV_CHIP_REVISION_5A_ES1 1u
#define CYDEV_CHIP_REVISION_5A_PRODUCTION 1u
#define CYDEV_CHIP_REVISION_5B_ES0 0u
#define CYDEV_CHIP_REVISION_5B_PRODUCTION 0u
#define CYDEV_CHIP_REVISION_FM3_PRODUCTION 0u
#define CYDEV_CHIP_REVISION_FM4_PRODUCTION 0u
#define CYDEV_CHIP_REVISION_PDL_FM0P_TYPE1_PRODUCTION 0u
#define CYDEV_CHIP_REVISION_PDL_FM0P_TYPE2_PRODUCTION 0u
#define CYDEV_CHIP_REVISION_PDL_FM0P_TYPE3_PRODUCTION 0u
#define CYDEV_CHIP_REVISION_USED CYDEV_CHIP_REVISION_4K_PRODUCTION
#define CYDEV_CHIP_REV_EXPECT CYDEV_CHIP_REVISION_USED
#define CYDEV_CONFIG_READ_ACCELERATOR 1
#define CYDEV_CONFIG_UNUSED_IO_AllowButWarn 0
#define CYDEV_CONFIG_UNUSED_IO CYDEV_CONFIG_UNUSED_IO_AllowButWarn
#define CYDEV_CONFIG_UNUSED_IO_AllowWithInfo 1
#define CYDEV_CONFIG_UNUSED_IO_Disallowed 2
#define CYDEV_CONFIGURATION_COMPRESSED 1
#define CYDEV_CONFIGURATION_MODE_COMPRESSED 0
#define CYDEV_CONFIGURATION_MODE CYDEV_CONFIGURATION_MODE_COMPRESSED
#define CYDEV_CONFIGURATION_MODE_DMA 2
#define CYDEV_CONFIGURATION_MODE_UNCOMPRESSED 1
#define CYDEV_DEBUG_PROTECT_KILL 4
#define CYDEV_DEBUG_PROTECT_OPEN 1
#define CYDEV_DEBUG_PROTECT CYDEV_DEBUG_PROTECT_OPEN
#define CYDEV_DEBUG_PROTECT_PROTECTED 2
#define CYDEV_DEBUGGING_DPS_Disable 3
#define CYDEV_DEBUGGING_DPS_SWD 2
#define CYDEV_DEBUGGING_DPS CYDEV_DEBUGGING_DPS_SWD
#define CYDEV_DEBUGGING_ENABLE 1
#define CYDEV_DFT_SELECT_CLK0 8u
#define CYDEV_DFT_SELECT_CLK1 9u
#define CYDEV_HEAP_SIZE 0x0A00
#define CYDEV_IMO_TRIMMED_BY_USB 0u
#define CYDEV_IMO_TRIMMED_BY_WCO 0u
#define CYDEV_IS_EXPORTING_CODE 0
#define CYDEV_IS_IMPORTING_CODE 0
#define CYDEV_PROJ_TYPE 0
#define CYDEV_PROJ_TYPE_BOOTLOADER 1
#define CYDEV_PROJ_TYPE_LAUNCHER 5
#define CYDEV_PROJ_TYPE_LOADABLE 2
#define CYDEV_PROJ_TYPE_LOADABLEANDBOOTLOADER 4
#define CYDEV_PROJ_TYPE_MULTIAPPBOOTLOADER 3
#define CYDEV_PROJ_TYPE_STANDARD 0
#define CYDEV_STACK_SIZE 0x0800
#define CYDEV_USE_BUNDLED_CMSIS 1
#define CYDEV_VARIABLE_VDDA 1
#define CYDEV_VDD 3.3
#define CYDEV_VDD_MV 3300
#define CYDEV_WDT_GENERATE_ISR 1u
#define CYIPBLOCK_m0s8cpussv3_VERSION 1
#define CYIPBLOCK_m0s8ioss_VERSION 1
#define CYIPBLOCK_m0s8lcd_VERSION 2
#define CYIPBLOCK_m0s8lpcomp_VERSION 2
#define CYIPBLOCK_m0s8pass4a_VERSION 1
#define CYIPBLOCK_m0s8peri_VERSION 1
#define CYIPBLOCK_m0s8scb_VERSION 2
#define CYIPBLOCK_m0s8tcpwm_VERSION 2
#define CYIPBLOCK_m0s8wco_VERSION 1
#define CYIPBLOCK_s8srsslt_VERSION 1
#define CYDEV_BOOTLOADER_ENABLE 0

#endif /* INCLUDED_CYFITTER_H */
