sparkfun/Spectacle_Motion_Board/Firmware/Spectacle_Servo_Control_Board/Spectacle_Servo_Control_Board.cydsn/codegentemp/PWM_2.h

/*******************************************************************************
* File Name: PWM_2.h
* Version 2.10
*
* Description:
*  This file provides constants and parameter values for the PWM_2
*  component.
*
* Note:
*  None
*
********************************************************************************
* Copyright 2013-2015, Cypress Semiconductor Corporation.  All rights reserved.
* You may use this file only in accordance with the license, terms, conditions,
* disclaimers, and limitations in the end user license agreement accompanying
* the software package with which this file was provided.
*******************************************************************************/

#if !defined(CY_TCPWM_PWM_2_H)
#define CY_TCPWM_PWM_2_H


#include "CyLib.h"
#include "cytypes.h"
#include "cyfitter.h"


/*******************************************************************************
* Internal Type defines
*******************************************************************************/

/* Structure to save state before go to sleep */
typedef struct
{
    uint8  enableState;
} PWM_2_BACKUP_STRUCT;


/*******************************************************************************
* Variables
*******************************************************************************/
extern uint8  PWM_2_initVar;


/***************************************
*   Conditional Compilation Parameters
****************************************/

#define PWM_2_CY_TCPWM_V2                    (CYIPBLOCK_m0s8tcpwm_VERSION == 2u)
#define PWM_2_CY_TCPWM_4000                  (CY_PSOC4_4000)

/* TCPWM Configuration */
#define PWM_2_CONFIG                         (7lu)

/* Quad Mode */
/* Parameters */
#define PWM_2_QUAD_ENCODING_MODES            (0lu)
#define PWM_2_QUAD_AUTO_START                (1lu)

/* Signal modes */
#define PWM_2_QUAD_INDEX_SIGNAL_MODE         (0lu)
#define PWM_2_QUAD_PHIA_SIGNAL_MODE          (3lu)
#define PWM_2_QUAD_PHIB_SIGNAL_MODE          (3lu)
#define PWM_2_QUAD_STOP_SIGNAL_MODE          (0lu)

/* Signal present */
#define PWM_2_QUAD_INDEX_SIGNAL_PRESENT      (0lu)
#define PWM_2_QUAD_STOP_SIGNAL_PRESENT       (0lu)

/* Interrupt Mask */
#define PWM_2_QUAD_INTERRUPT_MASK            (1lu)

/* Timer/Counter Mode */
/* Parameters */
#define PWM_2_TC_RUN_MODE                    (0lu)
#define PWM_2_TC_COUNTER_MODE                (0lu)
#define PWM_2_TC_COMP_CAP_MODE               (2lu)
#define PWM_2_TC_PRESCALER                   (0lu)

/* Signal modes */
#define PWM_2_TC_RELOAD_SIGNAL_MODE          (0lu)
#define PWM_2_TC_COUNT_SIGNAL_MODE           (3lu)
#define PWM_2_TC_START_SIGNAL_MODE           (0lu)
#define PWM_2_TC_STOP_SIGNAL_MODE            (0lu)
#define PWM_2_TC_CAPTURE_SIGNAL_MODE         (0lu)

/* Signal present */
#define PWM_2_TC_RELOAD_SIGNAL_PRESENT       (0lu)
#define PWM_2_TC_COUNT_SIGNAL_PRESENT        (0lu)
#define PWM_2_TC_START_SIGNAL_PRESENT        (0lu)
#define PWM_2_TC_STOP_SIGNAL_PRESENT         (0lu)
#define PWM_2_TC_CAPTURE_SIGNAL_PRESENT      (0lu)

/* Interrupt Mask */
#define PWM_2_TC_INTERRUPT_MASK              (1lu)

/* PWM Mode */
/* Parameters */
#define PWM_2_PWM_KILL_EVENT                 (0lu)
#define PWM_2_PWM_STOP_EVENT                 (0lu)
#define PWM_2_PWM_MODE                       (4lu)
#define PWM_2_PWM_OUT_N_INVERT               (0lu)
#define PWM_2_PWM_OUT_INVERT                 (0lu)
#define PWM_2_PWM_ALIGN                      (0lu)
#define PWM_2_PWM_RUN_MODE                   (0lu)
#define PWM_2_PWM_DEAD_TIME_CYCLE            (0lu)
#define PWM_2_PWM_PRESCALER                  (0lu)

/* Signal modes */
#define PWM_2_PWM_RELOAD_SIGNAL_MODE         (0lu)
#define PWM_2_PWM_COUNT_SIGNAL_MODE          (3lu)
#define PWM_2_PWM_START_SIGNAL_MODE          (0lu)
#define PWM_2_PWM_STOP_SIGNAL_MODE           (0lu)
#define PWM_2_PWM_SWITCH_SIGNAL_MODE         (0lu)

/* Signal present */
#define PWM_2_PWM_RELOAD_SIGNAL_PRESENT      (0lu)
#define PWM_2_PWM_COUNT_SIGNAL_PRESENT       (0lu)
#define PWM_2_PWM_START_SIGNAL_PRESENT       (0lu)
#define PWM_2_PWM_STOP_SIGNAL_PRESENT        (0lu)
#define PWM_2_PWM_SWITCH_SIGNAL_PRESENT      (0lu)

/* Interrupt Mask */
#define PWM_2_PWM_INTERRUPT_MASK             (1lu)


/***************************************
*    Initial Parameter Constants
***************************************/

/* Timer/Counter Mode */
#define PWM_2_TC_PERIOD_VALUE                (65535lu)
#define PWM_2_TC_COMPARE_VALUE               (65535lu)
#define PWM_2_TC_COMPARE_BUF_VALUE           (65535lu)
#define PWM_2_TC_COMPARE_SWAP                (0lu)

/* PWM Mode */
#define PWM_2_PWM_PERIOD_VALUE               (20000lu)
#define PWM_2_PWM_PERIOD_BUF_VALUE           (65535lu)
#define PWM_2_PWM_PERIOD_SWAP                (0lu)
#define PWM_2_PWM_COMPARE_VALUE              (1500lu)
#define PWM_2_PWM_COMPARE_BUF_VALUE          (65535lu)
#define PWM_2_PWM_COMPARE_SWAP               (0lu)


/***************************************
*    Enumerated Types and Parameters
***************************************/

#define PWM_2__LEFT 0
#define PWM_2__RIGHT 1
#define PWM_2__CENTER 2
#define PWM_2__ASYMMETRIC 3

#define PWM_2__X1 0
#define PWM_2__X2 1
#define PWM_2__X4 2

#define PWM_2__PWM 4
#define PWM_2__PWM_DT 5
#define PWM_2__PWM_PR 6

#define PWM_2__INVERSE 1
#define PWM_2__DIRECT 0

#define PWM_2__CAPTURE 2
#define PWM_2__COMPARE 0

#define PWM_2__TRIG_LEVEL 3
#define PWM_2__TRIG_RISING 0
#define PWM_2__TRIG_FALLING 1
#define PWM_2__TRIG_BOTH 2

#define PWM_2__INTR_MASK_TC 1
#define PWM_2__INTR_MASK_CC_MATCH 2
#define PWM_2__INTR_MASK_NONE 0
#define PWM_2__INTR_MASK_TC_CC 3

#define PWM_2__UNCONFIG 8
#define PWM_2__TIMER 1
#define PWM_2__QUAD 3
#define PWM_2__PWM_SEL 7

#define PWM_2__COUNT_UP 0
#define PWM_2__COUNT_DOWN 1
#define PWM_2__COUNT_UPDOWN0 2
#define PWM_2__COUNT_UPDOWN1 3


/* Prescaler */
#define PWM_2_PRESCALE_DIVBY1                ((uint32)(0u << PWM_2_PRESCALER_SHIFT))
#define PWM_2_PRESCALE_DIVBY2                ((uint32)(1u << PWM_2_PRESCALER_SHIFT))
#define PWM_2_PRESCALE_DIVBY4                ((uint32)(2u << PWM_2_PRESCALER_SHIFT))
#define PWM_2_PRESCALE_DIVBY8                ((uint32)(3u << PWM_2_PRESCALER_SHIFT))
#define PWM_2_PRESCALE_DIVBY16               ((uint32)(4u << PWM_2_PRESCALER_SHIFT))
#define PWM_2_PRESCALE_DIVBY32               ((uint32)(5u << PWM_2_PRESCALER_SHIFT))
#define PWM_2_PRESCALE_DIVBY64               ((uint32)(6u << PWM_2_PRESCALER_SHIFT))
#define PWM_2_PRESCALE_DIVBY128              ((uint32)(7u << PWM_2_PRESCALER_SHIFT))

/* TCPWM set modes */
#define PWM_2_MODE_TIMER_COMPARE             ((uint32)(PWM_2__COMPARE         <<  \
                                                                  PWM_2_MODE_SHIFT))
#define PWM_2_MODE_TIMER_CAPTURE             ((uint32)(PWM_2__CAPTURE         <<  \
                                                                  PWM_2_MODE_SHIFT))
#define PWM_2_MODE_QUAD                      ((uint32)(PWM_2__QUAD            <<  \
                                                                  PWM_2_MODE_SHIFT))
#define PWM_2_MODE_PWM                       ((uint32)(PWM_2__PWM             <<  \
                                                                  PWM_2_MODE_SHIFT))
#define PWM_2_MODE_PWM_DT                    ((uint32)(PWM_2__PWM_DT          <<  \
                                                                  PWM_2_MODE_SHIFT))
#define PWM_2_MODE_PWM_PR                    ((uint32)(PWM_2__PWM_PR          <<  \
                                                                  PWM_2_MODE_SHIFT))

/* Quad Modes */
#define PWM_2_MODE_X1                        ((uint32)(PWM_2__X1              <<  \
                                                                  PWM_2_QUAD_MODE_SHIFT))
#define PWM_2_MODE_X2                        ((uint32)(PWM_2__X2              <<  \
                                                                  PWM_2_QUAD_MODE_SHIFT))
#define PWM_2_MODE_X4                        ((uint32)(PWM_2__X4              <<  \
                                                                  PWM_2_QUAD_MODE_SHIFT))

/* Counter modes */
#define PWM_2_COUNT_UP                       ((uint32)(PWM_2__COUNT_UP        <<  \
                                                                  PWM_2_UPDOWN_SHIFT))
#define PWM_2_COUNT_DOWN                     ((uint32)(PWM_2__COUNT_DOWN      <<  \
                                                                  PWM_2_UPDOWN_SHIFT))
#define PWM_2_COUNT_UPDOWN0                  ((uint32)(PWM_2__COUNT_UPDOWN0   <<  \
                                                                  PWM_2_UPDOWN_SHIFT))
#define PWM_2_COUNT_UPDOWN1                  ((uint32)(PWM_2__COUNT_UPDOWN1   <<  \
                                                                  PWM_2_UPDOWN_SHIFT))

/* PWM output invert */
#define PWM_2_INVERT_LINE                    ((uint32)(PWM_2__INVERSE         <<  \
                                                                  PWM_2_INV_OUT_SHIFT))
#define PWM_2_INVERT_LINE_N                  ((uint32)(PWM_2__INVERSE         <<  \
                                                                  PWM_2_INV_COMPL_OUT_SHIFT))

/* Trigger modes */
#define PWM_2_TRIG_RISING                    ((uint32)PWM_2__TRIG_RISING)
#define PWM_2_TRIG_FALLING                   ((uint32)PWM_2__TRIG_FALLING)
#define PWM_2_TRIG_BOTH                      ((uint32)PWM_2__TRIG_BOTH)
#define PWM_2_TRIG_LEVEL                     ((uint32)PWM_2__TRIG_LEVEL)

/* Interrupt mask */
#define PWM_2_INTR_MASK_TC                   ((uint32)PWM_2__INTR_MASK_TC)
#define PWM_2_INTR_MASK_CC_MATCH             ((uint32)PWM_2__INTR_MASK_CC_MATCH)

/* PWM Output Controls */
#define PWM_2_CC_MATCH_SET                   (0x00u)
#define PWM_2_CC_MATCH_CLEAR                 (0x01u)
#define PWM_2_CC_MATCH_INVERT                (0x02u)
#define PWM_2_CC_MATCH_NO_CHANGE             (0x03u)
#define PWM_2_OVERLOW_SET                    (0x00u)
#define PWM_2_OVERLOW_CLEAR                  (0x04u)
#define PWM_2_OVERLOW_INVERT                 (0x08u)
#define PWM_2_OVERLOW_NO_CHANGE              (0x0Cu)
#define PWM_2_UNDERFLOW_SET                  (0x00u)
#define PWM_2_UNDERFLOW_CLEAR                (0x10u)
#define PWM_2_UNDERFLOW_INVERT               (0x20u)
#define PWM_2_UNDERFLOW_NO_CHANGE            (0x30u)

/* PWM Align */
#define PWM_2_PWM_MODE_LEFT                  (PWM_2_CC_MATCH_CLEAR        |   \
                                                         PWM_2_OVERLOW_SET           |   \
                                                         PWM_2_UNDERFLOW_NO_CHANGE)
#define PWM_2_PWM_MODE_RIGHT                 (PWM_2_CC_MATCH_SET          |   \
                                                         PWM_2_OVERLOW_NO_CHANGE     |   \
                                                         PWM_2_UNDERFLOW_CLEAR)
#define PWM_2_PWM_MODE_ASYM                  (PWM_2_CC_MATCH_INVERT       |   \
                                                         PWM_2_OVERLOW_SET           |   \
                                                         PWM_2_UNDERFLOW_CLEAR)

#if (PWM_2_CY_TCPWM_V2)
    #if(PWM_2_CY_TCPWM_4000)
        #define PWM_2_PWM_MODE_CENTER                (PWM_2_CC_MATCH_INVERT       |   \
                                                                 PWM_2_OVERLOW_NO_CHANGE     |   \
                                                                 PWM_2_UNDERFLOW_CLEAR)
    #else
        #define PWM_2_PWM_MODE_CENTER                (PWM_2_CC_MATCH_INVERT       |   \
                                                                 PWM_2_OVERLOW_SET           |   \
                                                                 PWM_2_UNDERFLOW_CLEAR)
    #endif /* (PWM_2_CY_TCPWM_4000) */
#else
    #define PWM_2_PWM_MODE_CENTER                (PWM_2_CC_MATCH_INVERT       |   \
                                                             PWM_2_OVERLOW_NO_CHANGE     |   \
                                                             PWM_2_UNDERFLOW_CLEAR)
#endif /* (PWM_2_CY_TCPWM_NEW) */

/* Command operations without condition */
#define PWM_2_CMD_CAPTURE                    (0u)
#define PWM_2_CMD_RELOAD                     (8u)
#define PWM_2_CMD_STOP                       (16u)
#define PWM_2_CMD_START                      (24u)

/* Status */
#define PWM_2_STATUS_DOWN                    (1u)
#define PWM_2_STATUS_RUNNING                 (2u)


/***************************************
*        Function Prototypes
****************************************/

void   PWM_2_Init(void);
void   PWM_2_Enable(void);
void   PWM_2_Start(void);
void   PWM_2_Stop(void);

void   PWM_2_SetMode(uint32 mode);
void   PWM_2_SetCounterMode(uint32 counterMode);
void   PWM_2_SetPWMMode(uint32 modeMask);
void   PWM_2_SetQDMode(uint32 qdMode);

void   PWM_2_SetPrescaler(uint32 prescaler);
void   PWM_2_TriggerCommand(uint32 mask, uint32 command);
void   PWM_2_SetOneShot(uint32 oneShotEnable);
uint32 PWM_2_ReadStatus(void);

void   PWM_2_SetPWMSyncKill(uint32 syncKillEnable);
void   PWM_2_SetPWMStopOnKill(uint32 stopOnKillEnable);
void   PWM_2_SetPWMDeadTime(uint32 deadTime);
void   PWM_2_SetPWMInvert(uint32 mask);

void   PWM_2_SetInterruptMode(uint32 interruptMask);
uint32 PWM_2_GetInterruptSourceMasked(void);
uint32 PWM_2_GetInterruptSource(void);
void   PWM_2_ClearInterrupt(uint32 interruptMask);
void   PWM_2_SetInterrupt(uint32 interruptMask);

void   PWM_2_WriteCounter(uint32 count);
uint32 PWM_2_ReadCounter(void);

uint32 PWM_2_ReadCapture(void);
uint32 PWM_2_ReadCaptureBuf(void);

void   PWM_2_WritePeriod(uint32 period);
uint32 PWM_2_ReadPeriod(void);
void   PWM_2_WritePeriodBuf(uint32 periodBuf);
uint32 PWM_2_ReadPeriodBuf(void);

void   PWM_2_WriteCompare(uint32 compare);
uint32 PWM_2_ReadCompare(void);
void   PWM_2_WriteCompareBuf(uint32 compareBuf);
uint32 PWM_2_ReadCompareBuf(void);

void   PWM_2_SetPeriodSwap(uint32 swapEnable);
void   PWM_2_SetCompareSwap(uint32 swapEnable);

void   PWM_2_SetCaptureMode(uint32 triggerMode);
void   PWM_2_SetReloadMode(uint32 triggerMode);
void   PWM_2_SetStartMode(uint32 triggerMode);
void   PWM_2_SetStopMode(uint32 triggerMode);
void   PWM_2_SetCountMode(uint32 triggerMode);

void   PWM_2_SaveConfig(void);
void   PWM_2_RestoreConfig(void);
void   PWM_2_Sleep(void);
void   PWM_2_Wakeup(void);


/***************************************
*             Registers
***************************************/

#define PWM_2_BLOCK_CONTROL_REG              (*(reg32 *) PWM_2_cy_m0s8_tcpwm_1__TCPWM_CTRL )
#define PWM_2_BLOCK_CONTROL_PTR              ( (reg32 *) PWM_2_cy_m0s8_tcpwm_1__TCPWM_CTRL )
#define PWM_2_COMMAND_REG                    (*(reg32 *) PWM_2_cy_m0s8_tcpwm_1__TCPWM_CMD )
#define PWM_2_COMMAND_PTR                    ( (reg32 *) PWM_2_cy_m0s8_tcpwm_1__TCPWM_CMD )
#define PWM_2_INTRRUPT_CAUSE_REG             (*(reg32 *) PWM_2_cy_m0s8_tcpwm_1__TCPWM_INTR_CAUSE )
#define PWM_2_INTRRUPT_CAUSE_PTR             ( (reg32 *) PWM_2_cy_m0s8_tcpwm_1__TCPWM_INTR_CAUSE )
#define PWM_2_CONTROL_REG                    (*(reg32 *) PWM_2_cy_m0s8_tcpwm_1__CTRL )
#define PWM_2_CONTROL_PTR                    ( (reg32 *) PWM_2_cy_m0s8_tcpwm_1__CTRL )
#define PWM_2_STATUS_REG                     (*(reg32 *) PWM_2_cy_m0s8_tcpwm_1__STATUS )
#define PWM_2_STATUS_PTR                     ( (reg32 *) PWM_2_cy_m0s8_tcpwm_1__STATUS )
#define PWM_2_COUNTER_REG                    (*(reg32 *) PWM_2_cy_m0s8_tcpwm_1__COUNTER )
#define PWM_2_COUNTER_PTR                    ( (reg32 *) PWM_2_cy_m0s8_tcpwm_1__COUNTER )
#define PWM_2_COMP_CAP_REG                   (*(reg32 *) PWM_2_cy_m0s8_tcpwm_1__CC )
#define PWM_2_COMP_CAP_PTR                   ( (reg32 *) PWM_2_cy_m0s8_tcpwm_1__CC )
#define PWM_2_COMP_CAP_BUF_REG               (*(reg32 *) PWM_2_cy_m0s8_tcpwm_1__CC_BUFF )
#define PWM_2_COMP_CAP_BUF_PTR               ( (reg32 *) PWM_2_cy_m0s8_tcpwm_1__CC_BUFF )
#define PWM_2_PERIOD_REG                     (*(reg32 *) PWM_2_cy_m0s8_tcpwm_1__PERIOD )
#define PWM_2_PERIOD_PTR                     ( (reg32 *) PWM_2_cy_m0s8_tcpwm_1__PERIOD )
#define PWM_2_PERIOD_BUF_REG                 (*(reg32 *) PWM_2_cy_m0s8_tcpwm_1__PERIOD_BUFF )
#define PWM_2_PERIOD_BUF_PTR                 ( (reg32 *) PWM_2_cy_m0s8_tcpwm_1__PERIOD_BUFF )
#define PWM_2_TRIG_CONTROL0_REG              (*(reg32 *) PWM_2_cy_m0s8_tcpwm_1__TR_CTRL0 )
#define PWM_2_TRIG_CONTROL0_PTR              ( (reg32 *) PWM_2_cy_m0s8_tcpwm_1__TR_CTRL0 )
#define PWM_2_TRIG_CONTROL1_REG              (*(reg32 *) PWM_2_cy_m0s8_tcpwm_1__TR_CTRL1 )
#define PWM_2_TRIG_CONTROL1_PTR              ( (reg32 *) PWM_2_cy_m0s8_tcpwm_1__TR_CTRL1 )
#define PWM_2_TRIG_CONTROL2_REG              (*(reg32 *) PWM_2_cy_m0s8_tcpwm_1__TR_CTRL2 )
#define PWM_2_TRIG_CONTROL2_PTR              ( (reg32 *) PWM_2_cy_m0s8_tcpwm_1__TR_CTRL2 )
#define PWM_2_INTERRUPT_REQ_REG              (*(reg32 *) PWM_2_cy_m0s8_tcpwm_1__INTR )
#define PWM_2_INTERRUPT_REQ_PTR              ( (reg32 *) PWM_2_cy_m0s8_tcpwm_1__INTR )
#define PWM_2_INTERRUPT_SET_REG              (*(reg32 *) PWM_2_cy_m0s8_tcpwm_1__INTR_SET )
#define PWM_2_INTERRUPT_SET_PTR              ( (reg32 *) PWM_2_cy_m0s8_tcpwm_1__INTR_SET )
#define PWM_2_INTERRUPT_MASK_REG             (*(reg32 *) PWM_2_cy_m0s8_tcpwm_1__INTR_MASK )
#define PWM_2_INTERRUPT_MASK_PTR             ( (reg32 *) PWM_2_cy_m0s8_tcpwm_1__INTR_MASK )
#define PWM_2_INTERRUPT_MASKED_REG           (*(reg32 *) PWM_2_cy_m0s8_tcpwm_1__INTR_MASKED )
#define PWM_2_INTERRUPT_MASKED_PTR           ( (reg32 *) PWM_2_cy_m0s8_tcpwm_1__INTR_MASKED )


/***************************************
*       Registers Constants
***************************************/

/* Mask */
#define PWM_2_MASK                           ((uint32)PWM_2_cy_m0s8_tcpwm_1__TCPWM_CTRL_MASK)

/* Shift constants for control register */
#define PWM_2_RELOAD_CC_SHIFT                (0u)
#define PWM_2_RELOAD_PERIOD_SHIFT            (1u)
#define PWM_2_PWM_SYNC_KILL_SHIFT            (2u)
#define PWM_2_PWM_STOP_KILL_SHIFT            (3u)
#define PWM_2_PRESCALER_SHIFT                (8u)
#define PWM_2_UPDOWN_SHIFT                   (16u)
#define PWM_2_ONESHOT_SHIFT                  (18u)
#define PWM_2_QUAD_MODE_SHIFT                (20u)
#define PWM_2_INV_OUT_SHIFT                  (20u)
#define PWM_2_INV_COMPL_OUT_SHIFT            (21u)
#define PWM_2_MODE_SHIFT                     (24u)

/* Mask constants for control register */
#define PWM_2_RELOAD_CC_MASK                 ((uint32)(PWM_2_1BIT_MASK        <<  \
                                                                            PWM_2_RELOAD_CC_SHIFT))
#define PWM_2_RELOAD_PERIOD_MASK             ((uint32)(PWM_2_1BIT_MASK        <<  \
                                                                            PWM_2_RELOAD_PERIOD_SHIFT))
#define PWM_2_PWM_SYNC_KILL_MASK             ((uint32)(PWM_2_1BIT_MASK        <<  \
                                                                            PWM_2_PWM_SYNC_KILL_SHIFT))
#define PWM_2_PWM_STOP_KILL_MASK             ((uint32)(PWM_2_1BIT_MASK        <<  \
                                                                            PWM_2_PWM_STOP_KILL_SHIFT))
#define PWM_2_PRESCALER_MASK                 ((uint32)(PWM_2_8BIT_MASK        <<  \
                                                                            PWM_2_PRESCALER_SHIFT))
#define PWM_2_UPDOWN_MASK                    ((uint32)(PWM_2_2BIT_MASK        <<  \
                                                                            PWM_2_UPDOWN_SHIFT))
#define PWM_2_ONESHOT_MASK                   ((uint32)(PWM_2_1BIT_MASK        <<  \
                                                                            PWM_2_ONESHOT_SHIFT))
#define PWM_2_QUAD_MODE_MASK                 ((uint32)(PWM_2_3BIT_MASK        <<  \
                                                                            PWM_2_QUAD_MODE_SHIFT))
#define PWM_2_INV_OUT_MASK                   ((uint32)(PWM_2_2BIT_MASK        <<  \
                                                                            PWM_2_INV_OUT_SHIFT))
#define PWM_2_MODE_MASK                      ((uint32)(PWM_2_3BIT_MASK        <<  \
                                                                            PWM_2_MODE_SHIFT))

/* Shift constants for trigger control register 1 */
#define PWM_2_CAPTURE_SHIFT                  (0u)
#define PWM_2_COUNT_SHIFT                    (2u)
#define PWM_2_RELOAD_SHIFT                   (4u)
#define PWM_2_STOP_SHIFT                     (6u)
#define PWM_2_START_SHIFT                    (8u)

/* Mask constants for trigger control register 1 */
#define PWM_2_CAPTURE_MASK                   ((uint32)(PWM_2_2BIT_MASK        <<  \
                                                                  PWM_2_CAPTURE_SHIFT))
#define PWM_2_COUNT_MASK                     ((uint32)(PWM_2_2BIT_MASK        <<  \
                                                                  PWM_2_COUNT_SHIFT))
#define PWM_2_RELOAD_MASK                    ((uint32)(PWM_2_2BIT_MASK        <<  \
                                                                  PWM_2_RELOAD_SHIFT))
#define PWM_2_STOP_MASK                      ((uint32)(PWM_2_2BIT_MASK        <<  \
                                                                  PWM_2_STOP_SHIFT))
#define PWM_2_START_MASK                     ((uint32)(PWM_2_2BIT_MASK        <<  \
                                                                  PWM_2_START_SHIFT))

/* MASK */
#define PWM_2_1BIT_MASK                      ((uint32)0x01u)
#define PWM_2_2BIT_MASK                      ((uint32)0x03u)
#define PWM_2_3BIT_MASK                      ((uint32)0x07u)
#define PWM_2_6BIT_MASK                      ((uint32)0x3Fu)
#define PWM_2_8BIT_MASK                      ((uint32)0xFFu)
#define PWM_2_16BIT_MASK                     ((uint32)0xFFFFu)

/* Shift constant for status register */
#define PWM_2_RUNNING_STATUS_SHIFT           (30u)


/***************************************
*    Initial Constants
***************************************/

#define PWM_2_CTRL_QUAD_BASE_CONFIG                                                          \
        (((uint32)(PWM_2_QUAD_ENCODING_MODES     << PWM_2_QUAD_MODE_SHIFT))       |\
         ((uint32)(PWM_2_CONFIG                  << PWM_2_MODE_SHIFT)))

#define PWM_2_CTRL_PWM_BASE_CONFIG                                                           \
        (((uint32)(PWM_2_PWM_STOP_EVENT          << PWM_2_PWM_STOP_KILL_SHIFT))   |\
         ((uint32)(PWM_2_PWM_OUT_INVERT          << PWM_2_INV_OUT_SHIFT))         |\
         ((uint32)(PWM_2_PWM_OUT_N_INVERT        << PWM_2_INV_COMPL_OUT_SHIFT))   |\
         ((uint32)(PWM_2_PWM_MODE                << PWM_2_MODE_SHIFT)))

#define PWM_2_CTRL_PWM_RUN_MODE                                                              \
            ((uint32)(PWM_2_PWM_RUN_MODE         << PWM_2_ONESHOT_SHIFT))
            
#define PWM_2_CTRL_PWM_ALIGN                                                                 \
            ((uint32)(PWM_2_PWM_ALIGN            << PWM_2_UPDOWN_SHIFT))

#define PWM_2_CTRL_PWM_KILL_EVENT                                                            \
             ((uint32)(PWM_2_PWM_KILL_EVENT      << PWM_2_PWM_SYNC_KILL_SHIFT))

#define PWM_2_CTRL_PWM_DEAD_TIME_CYCLE                                                       \
            ((uint32)(PWM_2_PWM_DEAD_TIME_CYCLE  << PWM_2_PRESCALER_SHIFT))

#define PWM_2_CTRL_PWM_PRESCALER                                                             \
            ((uint32)(PWM_2_PWM_PRESCALER        << PWM_2_PRESCALER_SHIFT))

#define PWM_2_CTRL_TIMER_BASE_CONFIG                                                         \
        (((uint32)(PWM_2_TC_PRESCALER            << PWM_2_PRESCALER_SHIFT))       |\
         ((uint32)(PWM_2_TC_COUNTER_MODE         << PWM_2_UPDOWN_SHIFT))          |\
         ((uint32)(PWM_2_TC_RUN_MODE             << PWM_2_ONESHOT_SHIFT))         |\
         ((uint32)(PWM_2_TC_COMP_CAP_MODE        << PWM_2_MODE_SHIFT)))
        
#define PWM_2_QUAD_SIGNALS_MODES                                                             \
        (((uint32)(PWM_2_QUAD_PHIA_SIGNAL_MODE   << PWM_2_COUNT_SHIFT))           |\
         ((uint32)(PWM_2_QUAD_INDEX_SIGNAL_MODE  << PWM_2_RELOAD_SHIFT))          |\
         ((uint32)(PWM_2_QUAD_STOP_SIGNAL_MODE   << PWM_2_STOP_SHIFT))            |\
         ((uint32)(PWM_2_QUAD_PHIB_SIGNAL_MODE   << PWM_2_START_SHIFT)))

#define PWM_2_PWM_SIGNALS_MODES                                                              \
        (((uint32)(PWM_2_PWM_SWITCH_SIGNAL_MODE  << PWM_2_CAPTURE_SHIFT))         |\
         ((uint32)(PWM_2_PWM_COUNT_SIGNAL_MODE   << PWM_2_COUNT_SHIFT))           |\
         ((uint32)(PWM_2_PWM_RELOAD_SIGNAL_MODE  << PWM_2_RELOAD_SHIFT))          |\
         ((uint32)(PWM_2_PWM_STOP_SIGNAL_MODE    << PWM_2_STOP_SHIFT))            |\
         ((uint32)(PWM_2_PWM_START_SIGNAL_MODE   << PWM_2_START_SHIFT)))

#define PWM_2_TIMER_SIGNALS_MODES                                                            \
        (((uint32)(PWM_2_TC_CAPTURE_SIGNAL_MODE  << PWM_2_CAPTURE_SHIFT))         |\
         ((uint32)(PWM_2_TC_COUNT_SIGNAL_MODE    << PWM_2_COUNT_SHIFT))           |\
         ((uint32)(PWM_2_TC_RELOAD_SIGNAL_MODE   << PWM_2_RELOAD_SHIFT))          |\
         ((uint32)(PWM_2_TC_STOP_SIGNAL_MODE     << PWM_2_STOP_SHIFT))            |\
         ((uint32)(PWM_2_TC_START_SIGNAL_MODE    << PWM_2_START_SHIFT)))
        
#define PWM_2_TIMER_UPDOWN_CNT_USED                                                          \
                ((PWM_2__COUNT_UPDOWN0 == PWM_2_TC_COUNTER_MODE)                  ||\
                 (PWM_2__COUNT_UPDOWN1 == PWM_2_TC_COUNTER_MODE))

#define PWM_2_PWM_UPDOWN_CNT_USED                                                            \
                ((PWM_2__CENTER == PWM_2_PWM_ALIGN)                               ||\
                 (PWM_2__ASYMMETRIC == PWM_2_PWM_ALIGN))               
        
#define PWM_2_PWM_PR_INIT_VALUE              (1u)
#define PWM_2_QUAD_PERIOD_INIT_VALUE         (0x8000u)



#endif /* End CY_TCPWM_PWM_2_H */

/* [] END OF FILE */
