sparkfun/Spectacle_Motion_Board/Firmware/Spectacle_Servo_Control_Board/Spectacle_Servo_Control_Board.cydsn/codegentemp/CyLib.h

/***************************************************************************//**
* \file CyLib.h
* \version 5.40
*
* \brief Provides a system API for the clocking, and interrupts.
*
* \note Documentation of the API's in this file is located in the System
* Reference Guide provided with PSoC Creator.
*
********************************************************************************
* \copyright
* Copyright 2008-2016, Cypress Semiconductor Corporation.  All rights reserved.
* You may use this file only in accordance with the license, terms, conditions,
* disclaimers, and limitations in the end user license agreement accompanying
* the software package with which this file was provided.
*******************************************************************************/

#if !defined(CY_BOOT_CYLIB_H)
#define CY_BOOT_CYLIB_H

#include "cytypes.h"
#include "cydevice_trm.h"
#include "CyLFClk.h"

#include <string.h>
#include <limits.h>
#include <ctype.h>


/**
* \addtogroup group_clocking

PSoC devices supported by PSoC Creator have flexible clocking capabilities. These clocking capabilities are
controlled in PSoC Creator by selections within the Design-Wide Resources settings, connectivity of clocking signals on
the design schematic, and API calls that can modify the clocking at runtime. The clocking API is provided in the CyLib.c
and CyLib.h files.

This section describes how PSoC Creator maps clocks onto the device and provides guidance on clocking methodologies that
are optimized for the PSoC architecture.


\section section_clocking_modes Power Modes
The IMO is available in Active and Sleep modes. It is automatically disabled/enabled for the proper Deep Sleep and
Hibernate mode entry/exit. The IMO is disabled during Deep Sleep and Hibernate modes.

The EXTCLK is available in Active and Sleep modes. The system will enter/exit Deep Sleep and Hibernate using external
clock. The device will re-enable the IMO if it was enabled before entering Deep Sleep or Hibernate, but it does not wait
for the IMO before starting the CPU. After entering Active mode, the IMO may take an additional 2 us to begin toggling.
The IMO will startup cleanly without glitches, but any dependency should account for this extra startup time. If
desired, firmware may increase wakeup hold-off using \ref CySysPmSetWakeupHoldoff() function to include this 2 us and
ensure the IMO is toggling by the time Active mode is reached.

The ILO is available in all modes except Hibernate and Stop.



\section section_clocking_connectivity Clock Connectivity
The PSoC architecture includes flexible clock generation logic. Refer to the Technical Reference Manual for a detailed
description of all the clocking sources available in a particular device. The usage of these various clocking sources
can be categorized by how those clocks are connected to elements of a design.

\section section_clocking_runtime_changing Changing Clocks in Run-time

\subsection section_clocking_runtime_changing_impact Impact on Components Operation
The components with internal clocks are directly impacted by the change of the system clock frequencies or sources. The
components clock frequencies obtained using design-time dividers. The run-time change of components clock source will
correspondingly change the internal component clock.  Refer to the component datasheet for the details.

\subsection section_clocking_runtime_adjust CyDelay APIs
The CyDelay APIs implement simple software-based delay loops. The loops compensate for system clock frequency. The
\ref CyDelayFreq() function must be called in order to adjust \ref CyDelay(), \ref CyDelayUs() and \ref CyDelayCycles()
functions to the new system clock value.

\subsection section_clocking_runtime_cache Cache Configuration
If the CPU clock frequency increases during device operation, the number of clock cycles cache will wait before sampling
data coming back from Flash should be adjusted. If the CPU clock frequency decreases, the number of clock cycles can be
also adjusted to improve CPU performance. See “CySysFlashSetWaitCycles()” for PSoC 4 for more information.

*/


/**
* \addtogroup group_clocking_hfclk High-Frequency Clocking API
* \ingroup group_clocking
* @{
*/
void CySysClkImoStart(void);
void CySysClkImoStop(void);
void CySysClkWriteHfclkDirect(uint32 clkSelect);

#if (CY_IP_IMO_TRIMMABLE_BY_WCO)
    void CySysClkImoEnableWcoLock(void);
    void CySysClkImoDisableWcoLock(void);
    uint32 CySysClkImoGetWcoLock(void);
#endif /* (CY_IP_IMO_TRIMMABLE_BY_WCO) */

#if (CY_IP_IMO_TRIMMABLE_BY_USB)
    void CySysClkImoEnableUsbLock(void);
    void CySysClkImoDisableUsbLock(void);
    uint32 CySysClkImoGetUsbLock(void);
#endif  /* (CY_IP_IMO_TRIMMABLE_BY_USB) */

#if (CY_IP_SRSSLT)
    void CySysClkWriteHfclkDiv(uint32 divider);
#endif /* (CY_IP_SRSSLT) */

void CySysClkWriteSysclkDiv(uint32 divider);
void CySysClkWriteImoFreq(uint32 freq);
uint32 CySysClkGetSysclkSource(void);
/** @} group_clocking_hfclk */


/**
* \addtogroup group_clocking_lfclk Low-Frequency Clocking API
* \ingroup group_clocking
* \detailed For PSoC 4 devices, the CyLFClk (low-frequency clock) APIs are located in separate files
* (CyLFClk.h/CyLFClk.c). See the CyLFClk Component Datasheet available from the System Reference Guides item of the
* PSoC Creator Help menu.
* @{
*/
/** @} group_clocking_lfclk */


/**
* \addtogroup group_clocking_eco External Crystal Oscillator (ECO) API
* \ingroup group_clocking
* @{
*/
#if (CY_IP_ECO)
    cystatus CySysClkEcoStart(uint32 timeoutUs);
    void     CySysClkEcoStop(void);
    uint32   CySysClkEcoReadStatus(void);

    #if (CY_IP_ECO_BLESS)
        void CySysClkWriteEcoDiv(uint32 divider);
    #endif /* (CY_IP_ECO_BLESS) */

    #if (CY_IP_ECO_SRSSV2)
        void CySysClkConfigureEcoTrim(uint32 wDTrim, uint32 aTrim, uint32 fTrim, uint32 rTrim, uint32 gTrim);
        cystatus CySysClkConfigureEcoDrive(uint32 freq, uint32 cLoad, uint32 esr, uint32 maxAmplitude);
    #endif /* (CY_IP_ECO_SRSSV2) */
#endif  /* (CY_IP_ECO) */
/** @} group_clocking_eco */


/**
* \addtogroup group_clocking_pll Phase-Locked Loop (PLL) API
* \ingroup group_clocking
* @{
*/
#if (CY_IP_SRSSV2 && CY_IP_PLL)
    cystatus CySysClkPllStart(uint32 pll, uint32 wait);
    void     CySysClkPllStop(uint32 pll);
    cystatus CySysClkPllSetPQ(uint32 pll, uint32 feedback, uint32 reference, uint32 current);
    cystatus CySysClkPllSetFrequency(uint32 pll, uint32 inputFreq, uint32 pllFreq, uint32 divider, uint32 freqTol);
    void     CySysClkPllSetSource(uint32 pll, uint32 source);
    cystatus CySysClkPllSetOutputDivider(uint32 pll, uint32 divider);
    void CySysClkPllSetBypassMode(uint32 pll, uint32 bypass);
    uint32 CySysClkPllGetUnlockStatus(uint32 pll);
    uint32 CySysClkPllGetLockStatus(uint32 pll);
#endif /* (CY_IP_SRSSV2 && CY_IP_PLL) */
/** @} group_clocking_pll */


/**
* \addtogroup group_api_lvd_functions Low Voltage Detection API
* @{
*/
#if(CY_IP_SRSSV2)
    void   CySysLvdEnable(uint32 threshold);
    void   CySysLvdDisable(void);
    uint32 CySysLvdGetInterruptSource(void);
    void   CySysLvdClearInterrupt(void);
#endif  /* (CY_IP_SRSSV2) */
/** @} group_api_lvd_functions */


/**
* \addtogroup group_interrupts Interrupt API
* \brief The APIs in this chapter apply to all architectures except as noted. The Interrupts API is provided in the
* CyLib.c and CyLib.h files. Refer also to the Interrupt component datasheet for more information about interrupts.
* @{
*/
cyisraddress CyIntSetSysVector(uint8 number, cyisraddress address);
cyisraddress CyIntGetSysVector(uint8 number);

cyisraddress CyIntSetVector(uint8 number, cyisraddress address);
cyisraddress CyIntGetVector(uint8 number);

void   CyIntSetPriority(uint8 number, uint8 priority);
uint8  CyIntGetPriority(uint8 number);

void   CyIntEnable(uint8 number);
uint8  CyIntGetState(uint8 number);
void   CyIntDisable(uint8 number);

void   CyIntSetPending(uint8 number);
void   CyIntClearPending(uint8 number);

uint32 CyDisableInts(void);
void   CyEnableInts(uint32 mask);
/** @} group_interrupts */


/**
* \addtogroup group_api_delay_functions Delay API
* @{
*/
/* Do not use these definitions directly in your application */
extern uint32 cydelayFreqHz;
extern uint32 cydelayFreqKhz;
extern uint8  cydelayFreqMhz;
extern uint32 cydelay32kMs;

void  CyDelay(uint32 milliseconds);
void  CyDelayUs(uint16 microseconds);
void  CyDelayFreq(uint32 freq);
void  CyDelayCycles(uint32 cycles);
/** @} group_api_delay_functions */


/**
* \addtogroup group_api_system_functions System API
* @{
*/
void  CySoftwareReset(void);
uint8 CyEnterCriticalSection(void);
void  CyExitCriticalSection(uint8 savedIntrStatus);
void  CyHalt(uint8 reason);
uint32 CySysGetResetReason(uint32 reason);
void CyGetUniqueId(uint32* uniqueId);

/* Default interrupt handler */
CY_ISR_PROTO(IntDefaultHandler);
/** @} group_api_system_functions */


/**
* \addtogroup group_api_systick_functions System Timer (SysTick) API
* @{
*/

typedef void (*cySysTickCallback)(void);

void CySysTickStart(void);
void CySysTickInit(void);
void CySysTickEnable(void);
void CySysTickStop(void);
void CySysTickEnableInterrupt(void);
void CySysTickDisableInterrupt(void);
void CySysTickSetReload(uint32 value);
uint32 CySysTickGetReload(void);
uint32 CySysTickGetValue(void);
cySysTickCallback CySysTickSetCallback(uint32 number, cySysTickCallback function);
cySysTickCallback CySysTickGetCallback(uint32 number);

#if(CY_SYSTICK_LFCLK_SOURCE)
    void CySysTickSetClockSource(uint32 clockSource);
#endif /* (CY_SYSTICK_LFCLK_SOURCE) */

uint32 CySysTickGetCountFlag(void);
void CySysTickClear(void);
extern uint32 CySysTickInitVar;
/** @} group_api_systick_functions */


#if (CY_IP_DMAC_PRESENT)
    void CySysSetRamAccessArbPriority(uint32 source);
    void CySysSetFlashAccessArbPriority(uint32 source);
    void CySysSetDmacAccessArbPriority(uint32 source);
    void CySysSetPeripheralAccessArbPriority(uint32 interfaceNumber, uint32 source);
#endif /* (CY_IP_DMAC_PRESENT) */


/**
* \addtogroup group_api_pvb_functions Programmable Voltage Block (PVB) API
* @{
*/
#if (CY_IP_PASS)
    void CySysPrbSetGlobalVrefSource(uint32 source);
    void CySysPrbSetBgGain(uint32 gain);
    void CySysPrbSetGlobalVrefVoltage(uint32 voltageTap);
    void CySysPrbEnableDeepsleepVddaRef(void);
    void CySysPrbDisableDeepsleepVddaRef(void);
    void CySysPrbEnableVddaRef(void);
    void CySysPrbDisableVddaRef(void);
    void CySysPrbSetBgBufferTrim(int32 bgTrim);
    int32 CySysPrbGetBgBufferTrim(void);
#endif /* (CY_IP_PASS) */
/** @} group_api_pvb_functions */


/***************************************
* API Constants
***************************************/


/*******************************************************************************
* Clock API Constants
*******************************************************************************/

/* CySysClkWriteHfclkDirect() - implementation definitions */
#if(CY_IP_SRSSV2)
    #define CY_SYS_CLK_SELECT_DIRECT_SEL_MASK           (( uint32 ) 0x07u)
    #define CY_SYS_CLK_SELECT_DIRECT_SEL_PARAM_MASK     (( uint32 ) 0x07u)

    #define CY_SYS_CLK_SELECT_HFCLK_SEL_SHIFT           (( uint32 ) 16u)

    #if (CY_IP_SRSSV2 && CY_IP_PLL)
        #define CY_SYS_CLK_SELECT_HFCLK_SEL_MASK            (( uint32 ) 3u << CY_SYS_CLK_SELECT_HFCLK_SEL_SHIFT)
    #else
        #define CY_SYS_CLK_SELECT_HFCLK_SEL_MASK            (( uint32 ) 0u )
    #endif /* (CY_IP_SRSSV2 && CY_IP_PLL) */

#else
    #define CY_SYS_CLK_SELECT_DIRECT_SEL_MASK           (( uint32 ) 0x03u)
    #define CY_SYS_CLK_SELECT_DIRECT_SEL_PARAM_MASK     (CY_SYS_CLK_SELECT_DIRECT_SEL_MASK)
    #define CY_SYS_CLK_SELECT_HFCLK_SEL_MASK            (( uint32 ) 0u )
#endif  /* (CY_IP_SRSSV2) */

/* CySysClkWriteHfclkDirect() - parameter definitions */
#define CY_SYS_CLK_HFCLK_IMO                            (0u)
#define CY_SYS_CLK_HFCLK_EXTCLK                         (1u)
#if (CY_IP_ECO)
    #define CY_SYS_CLK_HFCLK_ECO                        (2u)
#endif  /* (CY_IP_ECO) */

#if (CY_IP_PLL)
    #define CY_SYS_CLK_HFCLK_PLL0                       ((uint32) ((uint32) 2u << CY_SYS_CLK_SELECT_HFCLK_SEL_SHIFT))
    #define CY_SYS_CLK_HFCLK_PLL1                       ((uint32) ((uint32) 1u << CY_SYS_CLK_SELECT_HFCLK_SEL_SHIFT))
#endif  /* (CY_IP_PLL) */

/* CySysClkWriteSysclkDiv() - parameter definitions */
#define CY_SYS_CLK_SYSCLK_DIV1                          (0u)
#define CY_SYS_CLK_SYSCLK_DIV2                          (1u)
#define CY_SYS_CLK_SYSCLK_DIV4                          (2u)
#define CY_SYS_CLK_SYSCLK_DIV8                          (3u)
#if(CY_IP_SRSSV2)
    #define CY_SYS_CLK_SYSCLK_DIV16                     (4u)
    #define CY_SYS_CLK_SYSCLK_DIV32                     (5u)
    #define CY_SYS_CLK_SYSCLK_DIV64                     (6u)
    #define CY_SYS_CLK_SYSCLK_DIV128                    (7u)
#endif  /* (CY_IP_SRSSV2) */


/* CySysClkWriteSysclkDiv() - implementation definitions */
#if(CY_IP_SRSSV2)
    #define CY_SYS_CLK_SELECT_SYSCLK_DIV_SHIFT          (19u)
    #define CY_SYS_CLK_SELECT_SYSCLK_DIV_MASK           (( uint32 )0x07u)
#else
    #define CY_SYS_CLK_SELECT_SYSCLK_DIV_SHIFT          (6u)
    #define CY_SYS_CLK_SELECT_SYSCLK_DIV_MASK           (( uint32 )0x03u)
#endif  /* (CY_IP_SRSSV2) */


/* CySysClkPllSetSource() - implementation definitions */
#if(CY_IP_SRSSV2)
    #if (CY_IP_PLL)
        #define CY_SYS_CLK_SELECT_PLL_SHIFT(x)            (3u + (3u * (x)))
        #define CY_SYS_CLK_SELECT_PLL_MASK(x)             ((uint32) ((uint32) 0x07u << CY_SYS_CLK_SELECT_PLL_SHIFT((x))))
    #endif /* (CY_IP_PLL) */
#endif  /* (CY_IP_SRSSV2) */

/* CySysClkPllSetSource() - parameter definitions */
#if(CY_IP_SRSSV2)
    #if (CY_IP_PLL)
        #define CY_SYS_PLL_SOURCE_IMO                   (0u)
        #define CY_SYS_PLL_SOURCE_EXTCLK                (1u)
        #define CY_SYS_PLL_SOURCE_ECO                   (2u)
        #define CY_SYS_PLL_SOURCE_DSI0                  (4u)
        #define CY_SYS_PLL_SOURCE_DSI1                  (5u)
        #define CY_SYS_PLL_SOURCE_DSI2                  (6u)
        #define CY_SYS_PLL_SOURCE_DSI3                  (7u)
    #endif /* (CY_IP_PLL) */
#endif  /* (CY_IP_SRSSV2) */

/* CySysClkPllSetBypassMode() - parameter definitions */
#if(CY_IP_SRSSV2)
    #if (CY_IP_PLL)
        #define CY_SYS_PLL_BYPASS_AUTO         (0u)
        #define CY_SYS_PLL_BYPASS_PLL_REF      (2u)
        #define CY_SYS_PLL_BYPASS_PLL_OUT      (3u)
    #endif /* (CY_IP_PLL) */
#endif  /* (CY_IP_SRSSV2) */

/* CySysClkPllSetOutputDivider()/CySysClkPllSetFrequency() - parameters */
#if(CY_IP_SRSSV2)
    #if (CY_IP_PLL)
        #define CY_SYS_PLL_OUTPUT_DIVPASS               (0u)
        #define CY_SYS_PLL_OUTPUT_DIV2                  (1u)
        #define CY_SYS_PLL_OUTPUT_DIV4                  (2u)
        #define CY_SYS_PLL_OUTPUT_DIV8                  (3u)
    #endif /* (CY_IP_PLL) */
#endif  /* (CY_IP_SRSSV2) */


#if (CY_IP_SRSSV2 && CY_IP_PLL)

    /* Set of the PLL registers */
    typedef struct
    {
        uint32 config;
        uint32 status;
        uint32 test;
    } cy_sys_clk_pll_regs_struct;

    /* Array of the PLL registers */
    typedef struct
    {
        cy_sys_clk_pll_regs_struct pll[2u];
    } cy_sys_clk_pll_struct;


    /* CySysClkPllSetPQ() - implementation definitions */
    #define CY_SYS_CLK_PLL_CONFIG_FEEDBACK_DIV_SHIFT     (0u)
    #define CY_SYS_CLK_PLL_CONFIG_REFERENCE_DIV_SHIFT    (8u)
    #define CY_SYS_CLK_PLL_CONFIG_OUTPUT_DIV_SHIFT       (14u)
    #define CY_SYS_CLK_PLL_CONFIG_ICP_SEL_SHIFT          (16u)
    #define CY_SYS_CLK_PLL_CONFIG_BYPASS_SEL_SHIFT       (20u)

    #define CY_SYS_CLK_PLL_CONFIG_FEEDBACK_DIV_MASK     ((uint32) ((uint32) 0xFFu << CY_SYS_CLK_PLL_CONFIG_FEEDBACK_DIV_SHIFT))
    #define CY_SYS_CLK_PLL_CONFIG_REFERENCE_DIV_MASK    ((uint32) ((uint32) 0x3Fu << CY_SYS_CLK_PLL_CONFIG_REFERENCE_DIV_SHIFT))
    #define CY_SYS_CLK_PLL_CONFIG_OUTPUT_DIV_MASK       ((uint32) ((uint32) 0x03u << CY_SYS_CLK_PLL_CONFIG_OUTPUT_DIV_SHIFT))
    #define CY_SYS_CLK_PLL_CONFIG_ICP_SEL_MASK          ((uint32) ((uint32) 0x07u << CY_SYS_CLK_PLL_CONFIG_ICP_SEL_SHIFT))
    #define CY_SYS_CLK_PLL_CONFIG_BYPASS_SEL_MASK       ((uint32) ((uint32) 0x03u << CY_SYS_CLK_PLL_CONFIG_BYPASS_SEL_SHIFT))

    #define CY_SYS_CLK_PLL_CONFIG_BYPASS_SEL_PLL_REF    ((uint32) ((uint32) 2u << CY_SYS_CLK_PLL_CONFIG_BYPASS_SEL_SHIFT))

    #define CY_SYS_CLK_PLL_CONFIG_FEEDBACK_DIV_MIN      (4u)
    #define CY_SYS_CLK_PLL_CONFIG_FEEDBACK_DIV_MAX      (259u)
    #define CY_SYS_CLK_PLL_CONFIG_ICP_SEL_MIN           (2u)
    #define CY_SYS_CLK_PLL_CONFIG_ICP_SEL_MAX           (3u)
    #define CY_SYS_CLK_PLL_CONFIG_REFERENCE_DIV_MIN     (1u)
    #define CY_SYS_CLK_PLL_CONFIG_REFERENCE_DIV_MAX     (64u)

    /* CySysClkPllGetUnlockStatus() - implementation definitions */
    #define CY_SYS_CLK_PLL_TEST_UNLOCK_OCCURRED_SHIFT   (4u)
    #define CY_SYS_CLK_PLL_TEST_UNLOCK_OCCURRED_MASK    (( uint32 )(( uint32 )0x01u << CY_SYS_CLK_PLL_TEST_UNLOCK_OCCURRED_SHIFT))

    /* CySysClkPllSetFrequency() - implementation definitions */
    #define CY_SYS_CLK_PLL_QMINIP                       (1u)
    #define CY_SYS_CLK_PLL_FPFDMAX                      (3000u)

    #define CY_SYS_CLK_PLL_QMAXIP                       (64u)
    #define CY_SYS_CLK_PLL_FPFDMIN                      (1000u)

    #define CY_SYS_CLK_PLL_INVALID                      (0u)
    #define CY_SYS_CLK_PLL_CURRENT_DEFAULT              (2u)

    #define CY_SYS_CLK_PLL_INPUT_FREQ_MIN               (1000u)
    #define CY_SYS_CLK_PLL_INPUT_FREQ_MAX               (49152u)

    #define CY_SYS_CLK_PLL_OUTPUT_FREQ_MIN              (22500u)
    #define CY_SYS_CLK_PLL_OUTPUT_FREQ_MAX              (49152u)

    /* CySysClkPllStart() / CySysClkPllStop() - implementation definitions */
    #define CY_SYS_CLK_PLL_STATUS_LOCKED                (1u)
    #define CY_SYS_CLK_PLL_MIN_STARTUP_US               (5u)
    #define CY_SYS_CLK_PLL_MAX_STARTUP_US               (255u)

    #define CY_SYS_CLK_PLL_CONFIG_ENABLE                ((uint32) ((uint32) 1u << 31u))
    #define CY_SYS_CLK_PLL_CONFIG_ISOLATE               ((uint32) ((uint32) 1u << 30u))

#endif /* (CY_IP_SRSSV2 && CY_IP_PLL) */

/* CySysClkWriteImoFreq() - implementation definitions */
#if(CY_IP_SRSSV2)
    #define CY_SYS_CLK_IMO_MAX_FREQ_MHZ                 (48u)
    #define CY_SYS_CLK_IMO_MIN_FREQ_MHZ                 (3u)

    #define CY_SYS_CLK_IMO_TEMP_FREQ_MHZ                (24u)
    #define CY_SYS_CLK_IMO_TEMP_FREQ_TRIM2              (0x19u)     /* Corresponds to 24 MHz */

    #define CY_SYS_CLK_IMO_BOUNDARY_FREQ_MHZ            (43u)
    #define CY_SYS_CLK_IMO_BOUNDARY_FREQ_TRIM2          (0x30u)     /* Corresponds to 43 MHz */

    #define CY_SYS_CLK_IMO_FREQ_TIMEOUT_CYCLES          (5u)
    #define CY_SYS_CLK_IMO_TRIM_TIMEOUT_US              (5u)
    #define CY_SYS_CLK_IMO_FREQ_TABLE_SIZE              (46u)
    #define CY_SYS_CLK_IMO_FREQ_TABLE_OFFSET            (3u)
    #define CY_SYS_CLK_IMO_FREQ_BITS_MASK               (( uint32 )0x3Fu)
    #define CY_SYS_CLK_IMO_FREQ_CLEAR                   (( uint32 )(CY_SYS_CLK_IMO_FREQ_BITS_MASK << 8u))
    #define CY_SYS_CLK_IMO_TRIM4_GAIN_MASK				(( uint32 )0x1Fu)
	#define CY_SYS_CLK_IMO_TRIM4_WCO_GAIN               (( uint32 ) 12u)
    #define CY_SYS_CLK_IMO_TRIM4_USB_GAIN               (( uint32 ) 8u)

#if(CY_IP_IMO_TRIMMABLE_BY_USB)
    #define CY_SYS_CLK_USBDEVv2_CR1_ENABLE_LOCK         (( uint32 )0x02u)
#endif /* (CY_IP_IMO_TRIMMABLE_BY_USB) */

#else
    #define CY_SYS_CLK_IMO_MIN_FREQ_MHZ                 (24u)
    #define CY_SYS_CLK_IMO_MAX_FREQ_MHZ                 (48u)
    #define CY_SYS_CLK_IMO_STEP_SIZE_MASK               (0x03u)
    #define CY_SYS_CLK_IMO_TRIM1_OFFSET_MASK            (( uint32 )(0xFFu))
    #define CY_SYS_CLK_IMO_TRIM2_FSOFFSET_MASK          (( uint32 )(0x07u))
    #define CY_SYS_CLK_IMO_TRIM3_VALUES_MASK            (( uint32 )(0x7Fu))
    #define CY_SYS_CLK_IMO_SELECT_FREQ_MASK             (( uint32 )(0x07u))
    #define CY_SYS_CLK_IMO_SELECT_FREQ_SHIFT            (( uint32 )(0x02u))
    #define CY_SYS_CLK_IMO_SELECT_24MHZ                 (( uint32 )(0x00u))

    #define CY_SYS_CLK_IMO_TRIM_DELAY_US                (( uint32 )(50u))
    #define CY_SYS_CLK_IMO_TRIM_DELAY_CYCLES            (( uint32 )(50u))
#endif  /* (CY_IP_SRSSV2) */

/* CySysClkImoEnableUsbLock(void) -  - implementation definitions */
#if(CY_IP_IMO_TRIMMABLE_BY_USB)
    #define CY_SYS_CLK_USBDEVv2_CR1_ENABLE_LOCK         (( uint32 )0x02u)
#endif /* (CY_IP_IMO_TRIMMABLE_BY_USB) */

#if (CY_IP_IMO_TRIMMABLE_BY_WCO && CY_IP_IMO_TRIMMABLE_BY_USB)
    #define CY_SYS_CLK_OSCINTF_CTL_PORT_SEL_MASK        (( uint32 )0x01u)
    #define CY_SYS_CLK_OSCINTF_CTL_PORT_SEL_USB         (( uint32 )0x00u)
    #define CY_SYS_CLK_OSCINTF_CTL_PORT_SEL_WCO         (( uint32 )0x01u)
#endif /* (CY_IP_IMO_TRIMMABLE_BY_WCO && CY_IP_IMO_TRIMMABLE_BY_USB) */


#if(CY_IP_SRSSV2)
        /* Conversion between CySysClkWriteImoFreq() parameter and register's value */
        extern const uint8 cyImoFreqMhz2Reg[CY_SYS_CLK_IMO_FREQ_TABLE_SIZE];
#endif /* (CY_IP_SRSSV2) */


/* CySysClkImoStart()/CySysClkImoStop() - implementation definitions */
#define CY_SYS_CLK_IMO_CONFIG_ENABLE                    (( uint32 )(( uint32 )0x01u << 31u))



#if(CY_IP_SRSSLT)
    /* CySysClkWriteHfclkDiv() - parameter definitions */
    #define CY_SYS_CLK_HFCLK_DIV_NODIV                  (0u)
    #define CY_SYS_CLK_HFCLK_DIV_2                      (1u)
    #define CY_SYS_CLK_HFCLK_DIV_4                      (2u)
    #define CY_SYS_CLK_HFCLK_DIV_8                      (3u)

    /* CySysClkWriteHfclkDiv() - implementation definitions */
    #define CY_SYS_CLK_SELECT_HFCLK_DIV_SHIFT           (2u)
    #define CY_SYS_CLK_SELECT_HFCLK_DIV_MASK            (( uint32 )0x03u)
#endif  /* (CY_IP_SRSSLT) */


/* Operating source for Pump clock */
#if(CY_IP_SRSSV2)
    #define CY_SYS_CLK_IMO_CONFIG_PUMP_SEL_SHIFT        (25u)
    #define CY_SYS_CLK_IMO_CONFIG_PUMP_SEL_MASK         ((uint32) 0x07u)
    #define CY_SYS_CLK_IMO_CONFIG_PUMP_SEL_IMO          (1u)

	#define CY_SYS_CLK_IMO_CONFIG_PUMP_OSC              (( uint32 )(( uint32 )0x01u << 22u))
#else /* CY_IP_SRSSLT */
    #define CY_SYS_CLK_SELECT_PUMP_SEL_SHIFT            (4u)
    #define CY_SYS_CLK_SELECT_PUMP_SEL_MASK             ((uint32) 0x03u)
    #define CY_SYS_CLK_SELECT_PUMP_SEL_IMO              (1u)
#endif  /* (CY_IP_SRSSLT) */


#if (CY_IP_ECO_BLESS)
    /* Radio configuration register */
    #define CY_SYS_XTAL_BLESS_RF_CONFIG_RF_ENABLE       (( uint32 )0x01u)

    /* RFCTRL mode transition control */
    #define CY_SYS_XTAL_BLERD_DBUS_XTAL_ENABLE          (( uint32 )(( uint32 )0x01u << 15u))

    /* XO is oscillating status */
    #define CY_SYS_XTAL_BLERD_FSM_XO_AMP_DETECT         (( uint32 )0x01u)

    /* BB bump configuration 2 */
    #define CY_SYS_XTAL_BLERD_BB_XO_CAPTRIM_X1_MASK     (( uint32 )(( uint32 )0x7Fu <<  8u))
    #define CY_SYS_XTAL_BLERD_BB_XO_CAPTRIM_X2_MASK     (( uint32 )(( uint32 )0x7Fu <<  0u))
    #define CY_SYS_XTAL_BLERD_BB_XO_CAPTRIM_X1_ADD_CAP  (( uint32 )(( uint32 )0x01u << 15u))
    #define CY_SYS_XTAL_BLERD_BB_XO_CAPTRIM_X2_ADD_CAP  (( uint32 )(( uint32 )0x01u <<  7u))

    /* BB bump configuration 1 */
    #define CY_SYS_XTAL_BLERD_BB_XO_TRIM                ((uint32) 0x2002u)


    /**
    * \addtogroup group_api_eco
    * @{
    */
     #define CY_SYS_CLK_ECO_DIV1    ((uint32) 0x00)     /**< CySysClkWriteEcoDiv(): HFCLK = ECO / 1 */
     #define CY_SYS_CLK_ECO_DIV2    ((uint32) 0x01)     /**< CySysClkWriteEcoDiv(): HFCLK = ECO / 2 */
     #define CY_SYS_CLK_ECO_DIV4    ((uint32) 0x02)     /**< CySysClkWriteEcoDiv(): HFCLK = ECO / 4 */
     #define CY_SYS_CLK_ECO_DIV8    ((uint32) 0x03)     /**< CySysClkWriteEcoDiv(): HFCLK = ECO / 8 */
    /** @} group_api_eco */

    /* CySysClkWriteEcoDiv() - implementation definitions */
    #define CY_SYS_CLK_XTAL_CLK_DIV_MASK                ((uint32) 0x03)
#endif  /* (CY_IP_ECO_BLESS) */
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
